feelepxyz/dass/docs/original-drawing/cutlist.png

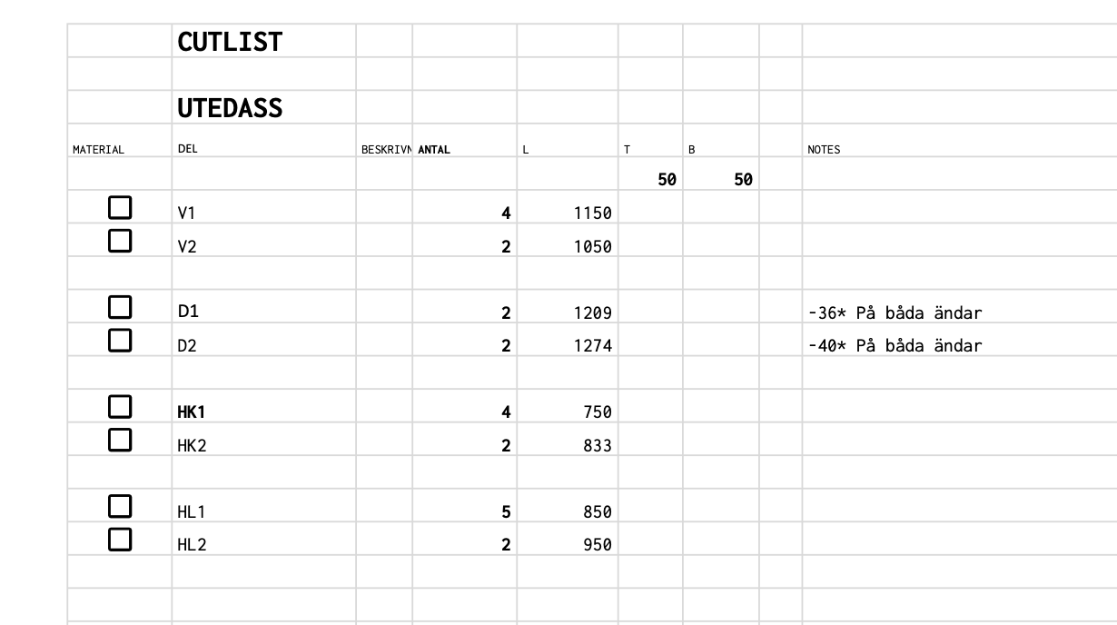
docs/original-drawing/cutlist.png
