feelepxyz/dass/docs/original-drawing/drawing-above.png

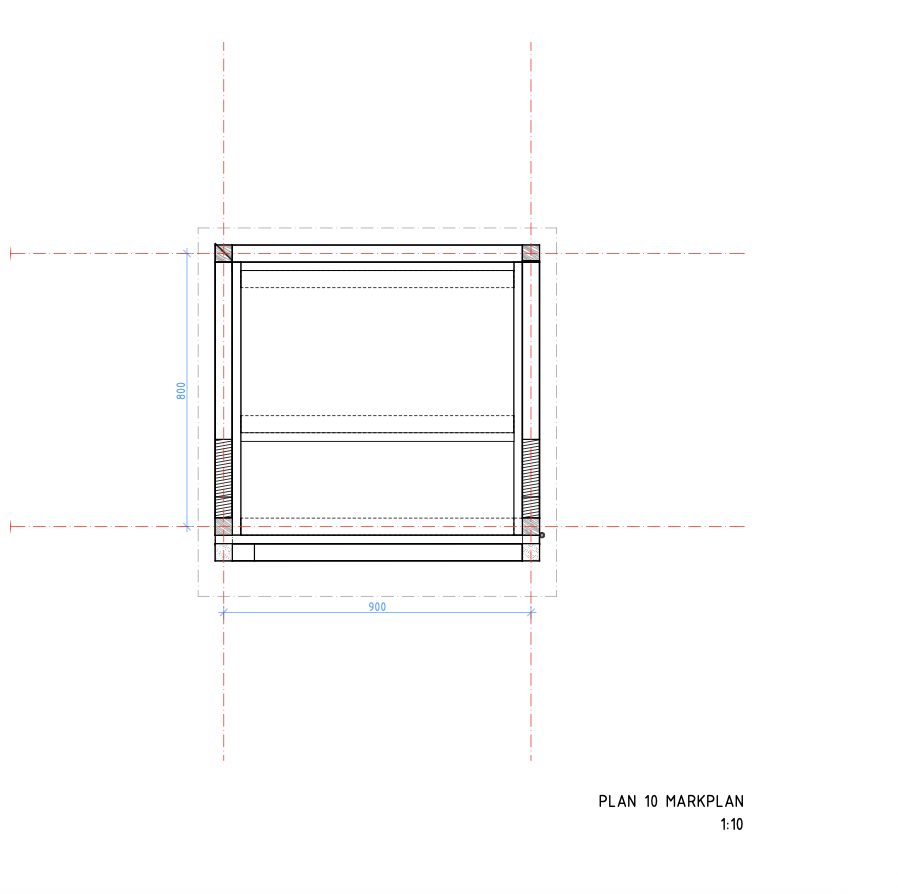
docs/original-drawing/drawing-above.png
