feelepxyz/dass/docs/original-drawing/render-target2.png

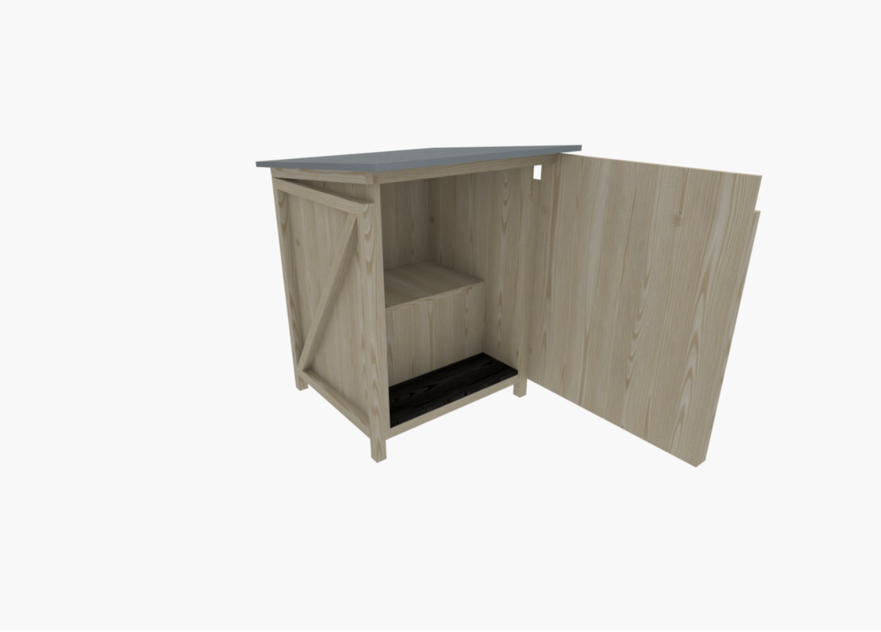
docs/original-drawing/render-target2.png
