feelepxyz/dass/docs/original-drawing/render-target.png

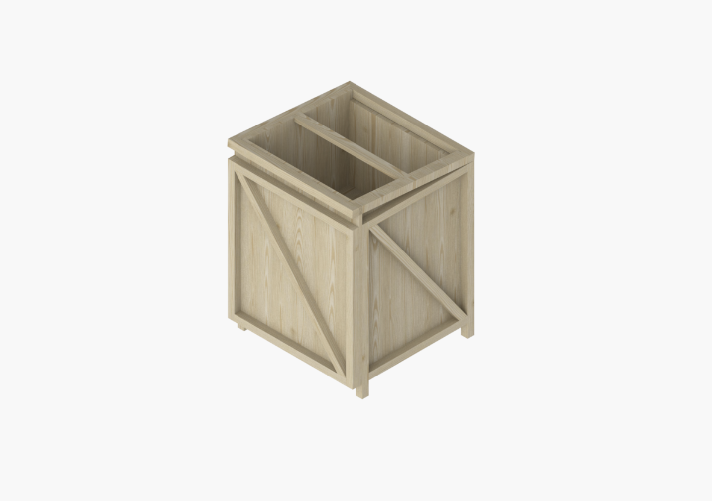
docs/original-drawing/render-target.png
