feelepxyz/dass/web/media/progress/cutting-poster.jpg

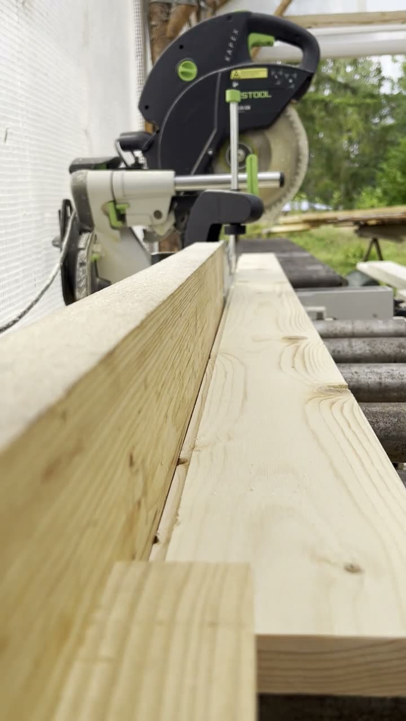
web/media/progress/cutting-poster.jpg
