feelepxyz/dass/web/media/progress/sides and floor.jpeg

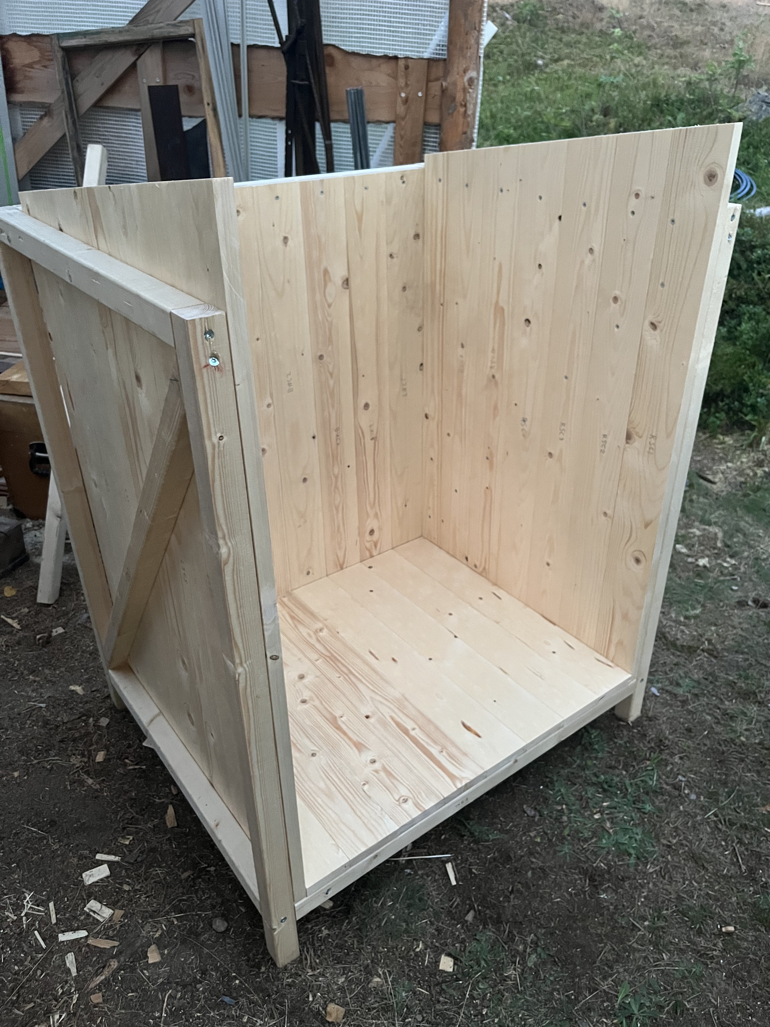
web/media/progress/sides and floor.jpeg
