feelepxyz/dass/build/dass-closed.png

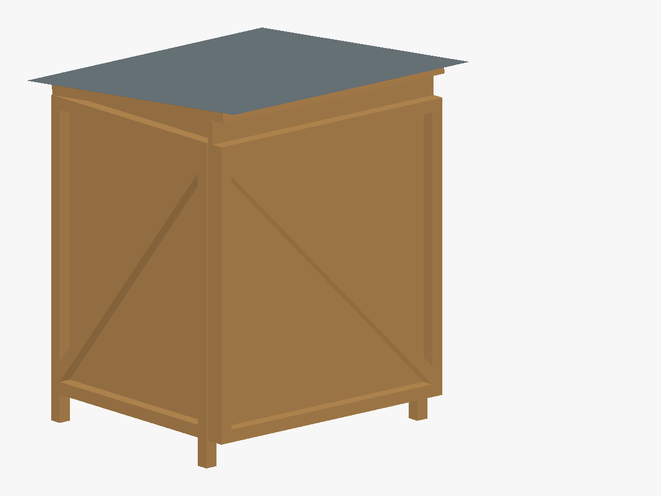
build/dass-closed.png
