feelepxyz/dass/build/dass-open.png

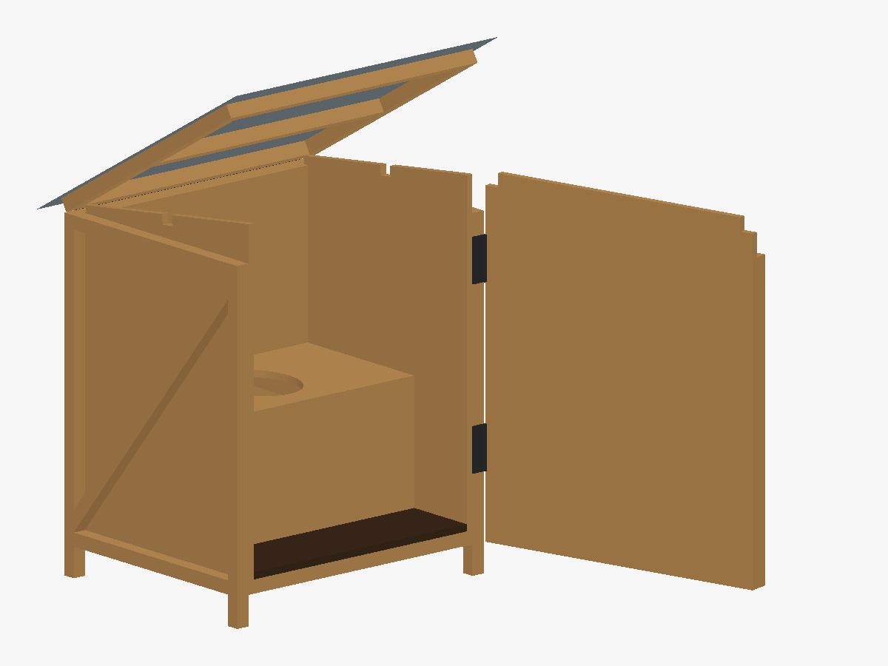
build/dass-open.png
