feelepxyz/dass/build/renders/closed-above.png

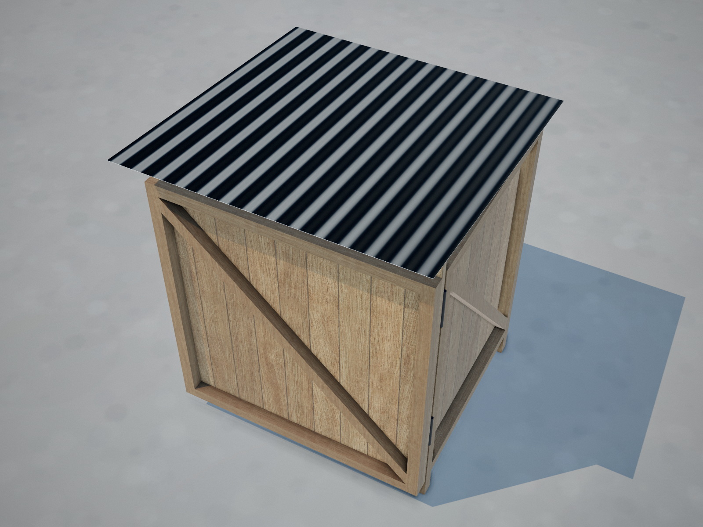
build/renders/closed-above.png
