feelepxyz/dass/build/renders/closed-front-left.png

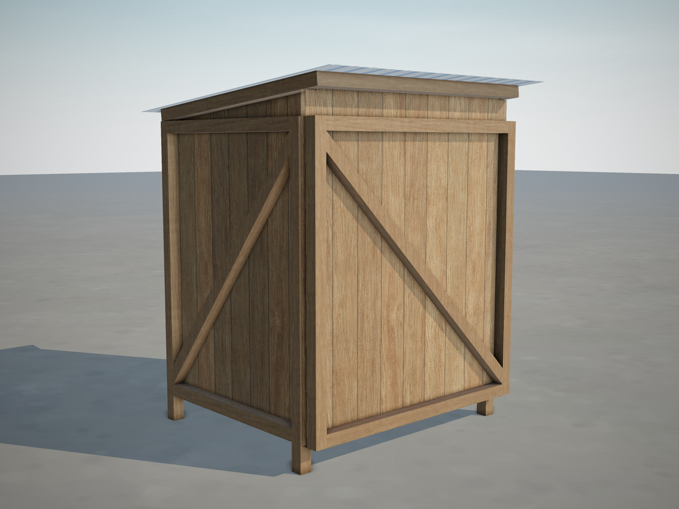
build/renders/closed-front-left.png
