feelepxyz/dass/build/renders/closed-hero.png

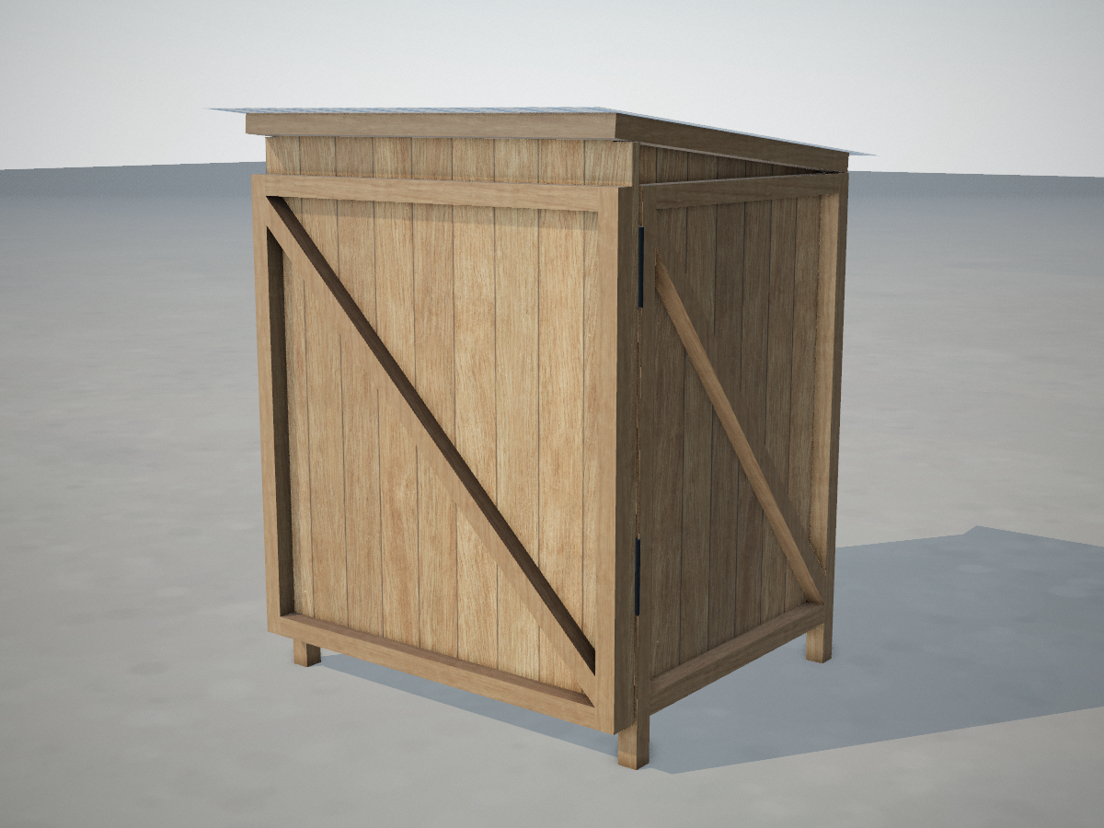
build/renders/closed-hero.png
