feelepxyz/dass/build/renders/closed-low.png

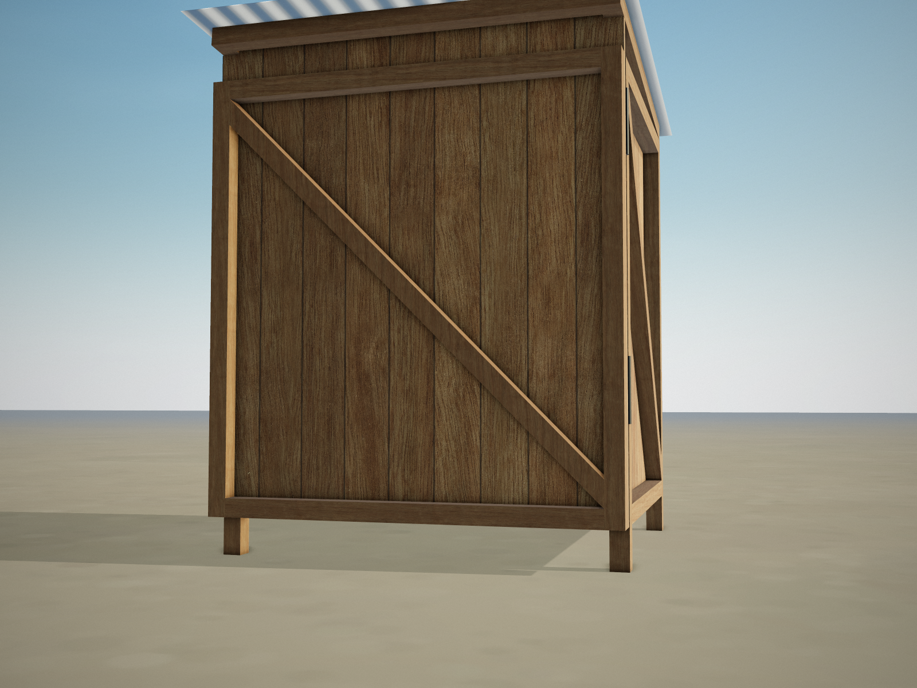
build/renders/closed-low.png
