feelepxyz/dass/build/renders/drawing-closed.png

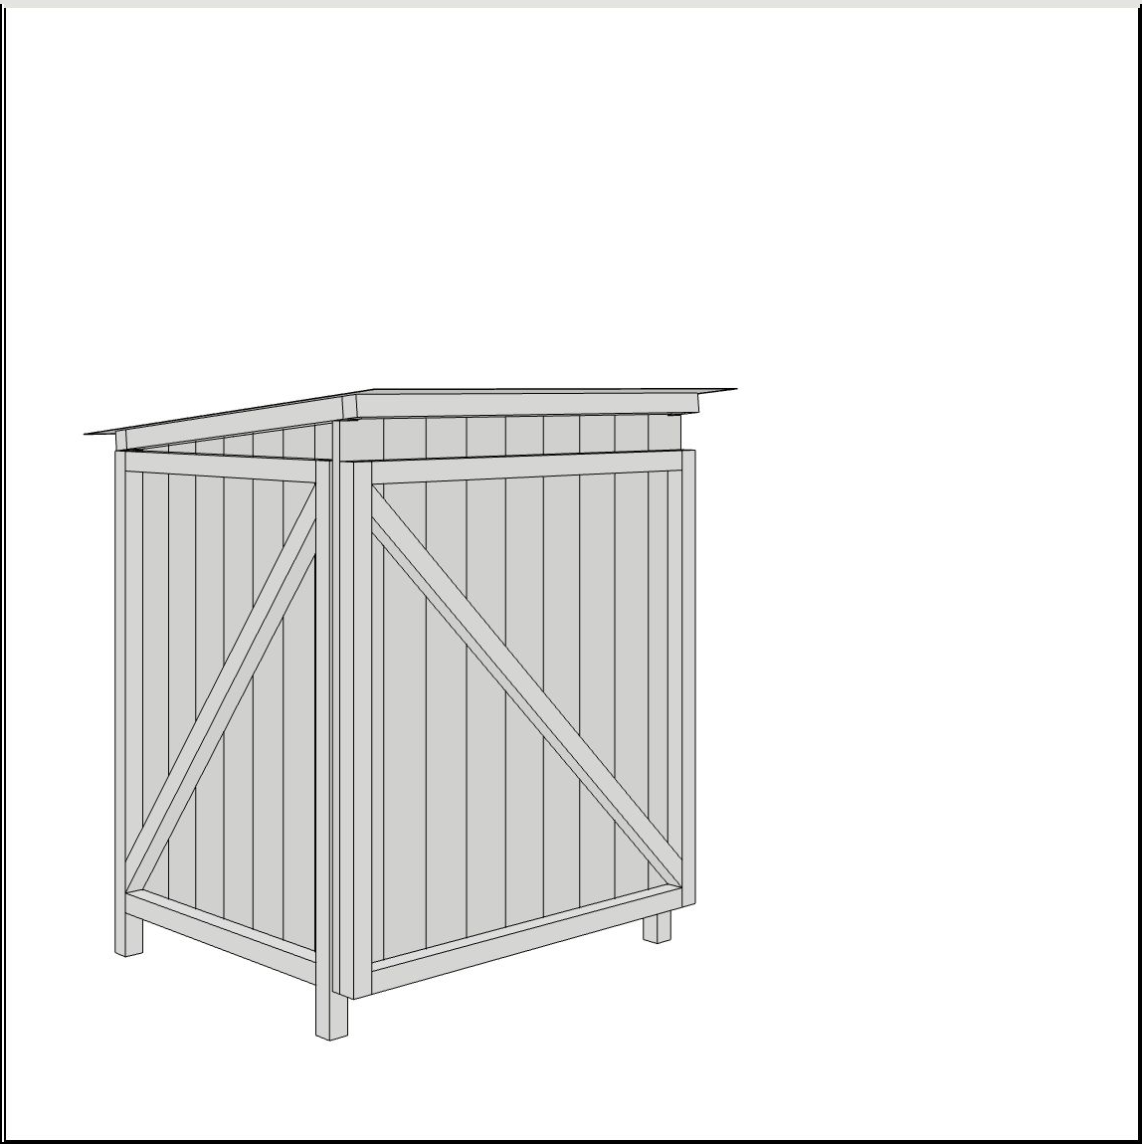
build/renders/drawing-closed.png
