feelepxyz/dass/build/renders/drawing-open.png

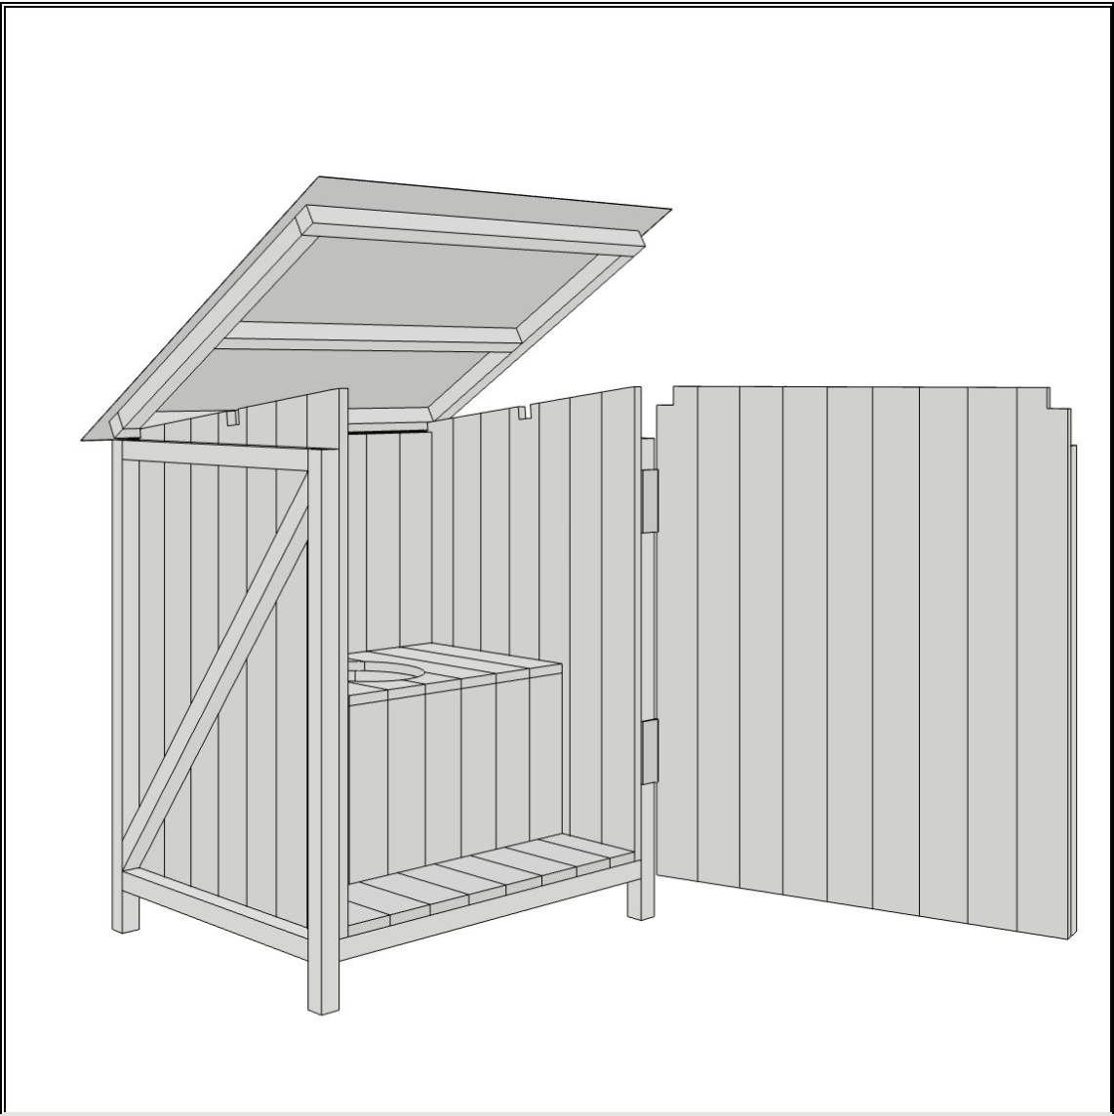
build/renders/drawing-open.png
