feelepxyz/dass/build/renders/flat-back.png

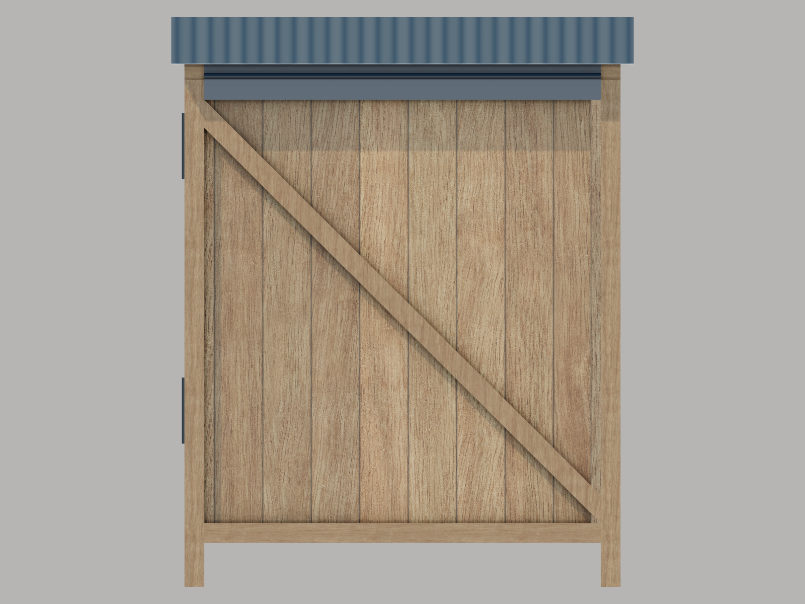
build/renders/flat-back.png
