feelepxyz/dass/build/renders/flat-bottom.png

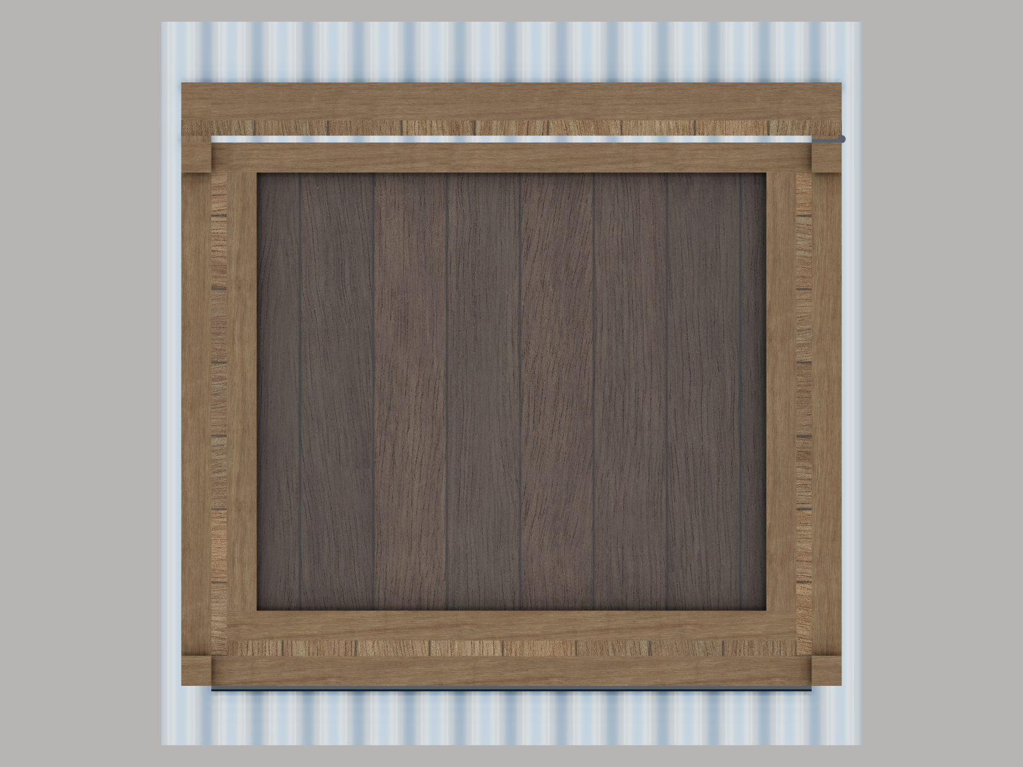
build/renders/flat-bottom.png
