feelepxyz/dass/build/renders/flat-front-open.png

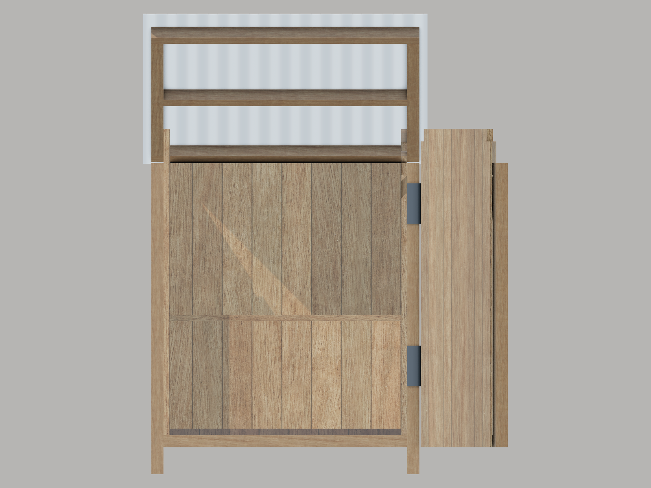
build/renders/flat-front-open.png
