feelepxyz/dass/build/renders/flat-front.png

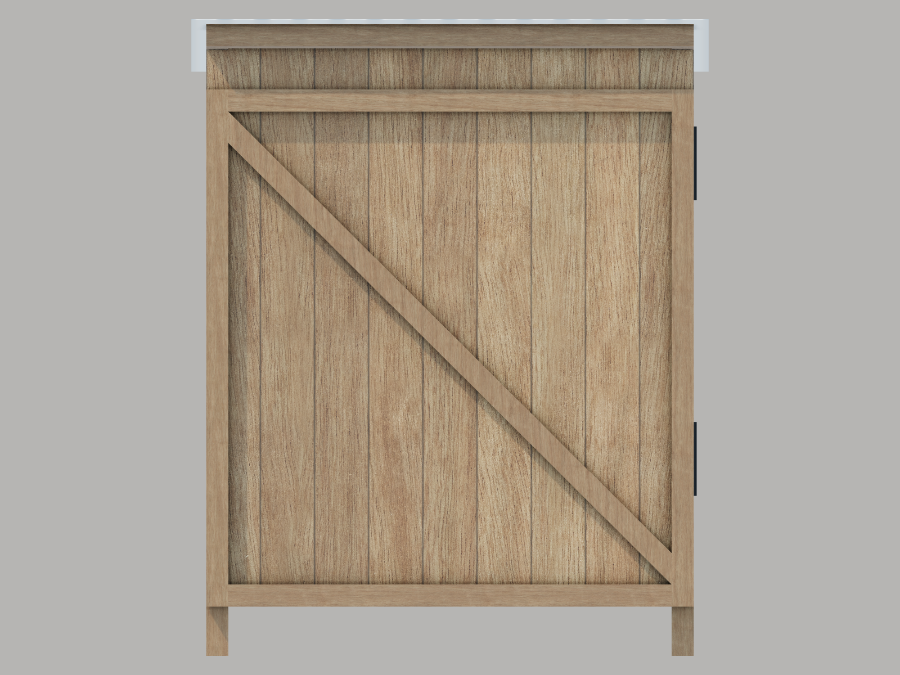
build/renders/flat-front.png
