feelepxyz/dass/build/renders/flat-left.png

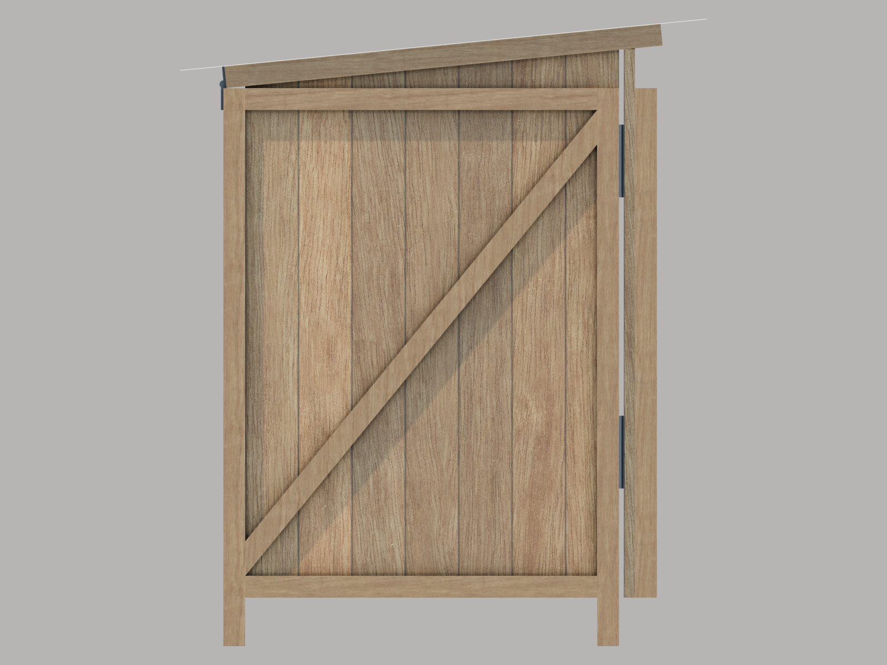
build/renders/flat-left.png
