feelepxyz/dass/build/renders/flat-right.png

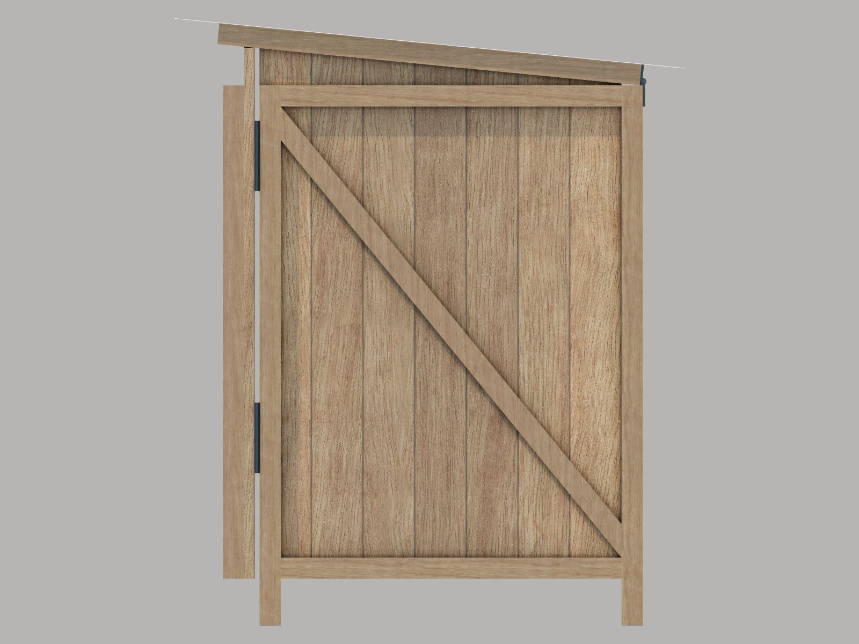
build/renders/flat-right.png
