feelepxyz/dass/build/renders/flat-top.png

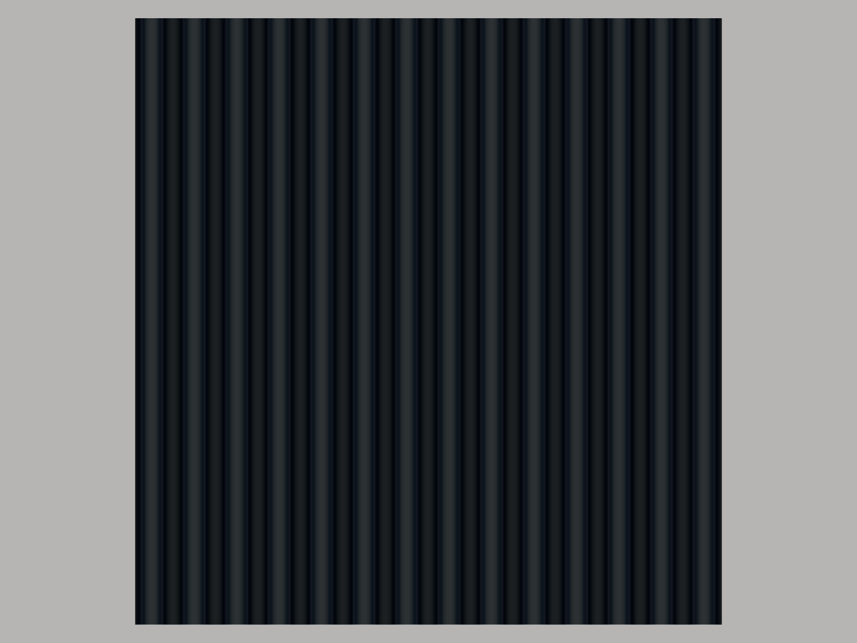
build/renders/flat-top.png
