feelepxyz/dass/build/renders/open-doorway.png

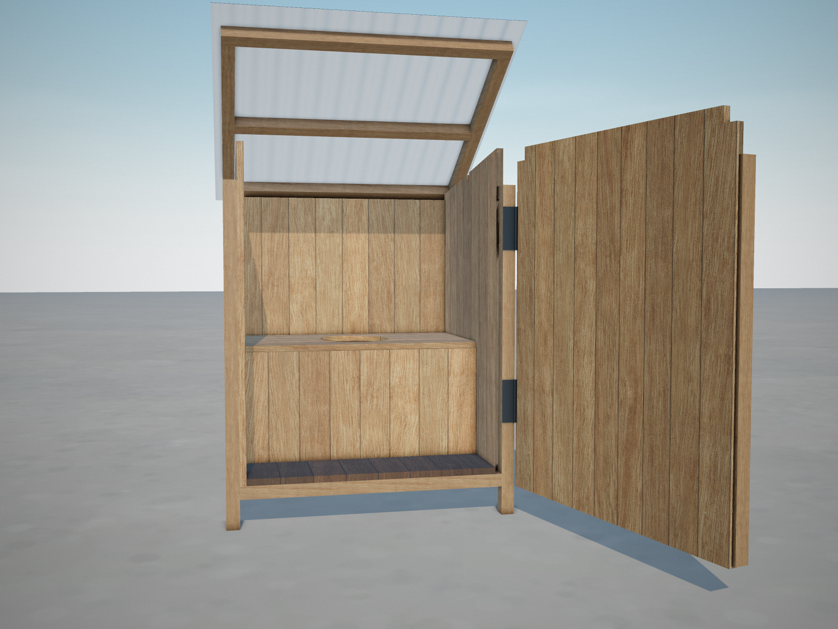
build/renders/open-doorway.png
