feelepxyz/dass/build/renders/open-hero.png

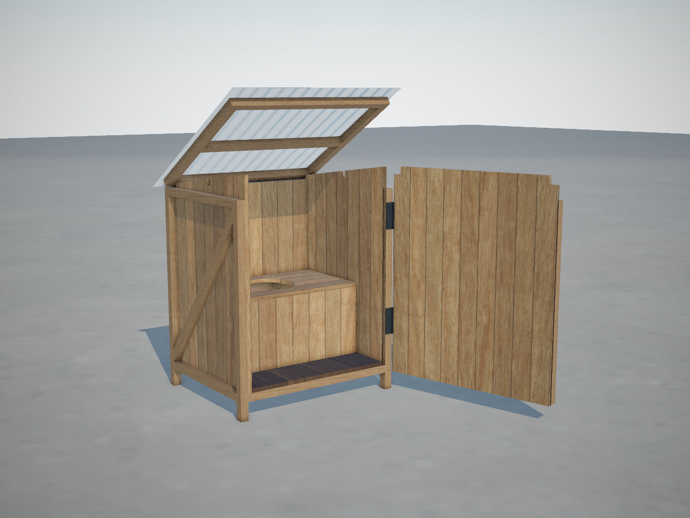
build/renders/open-hero.png
