feelepxyz/dass/build/renders/open-interior.png

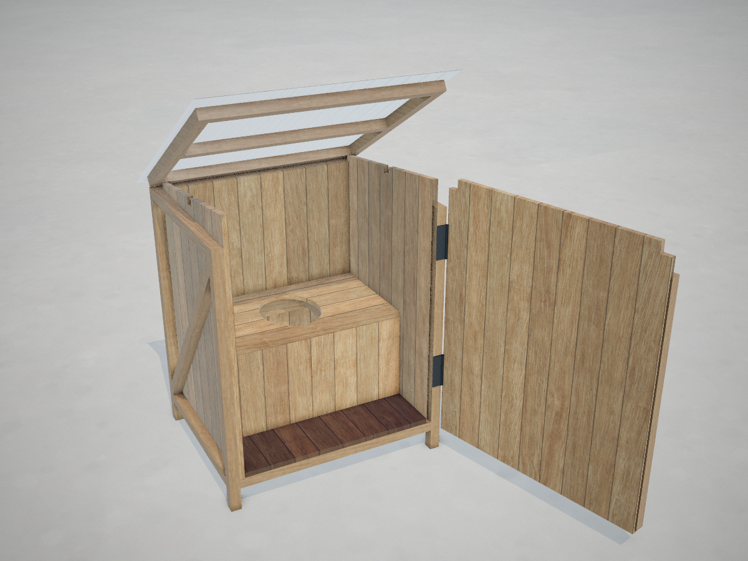
build/renders/open-interior.png
