feelepxyz/dass/build/renders/open-rear-quarter.png

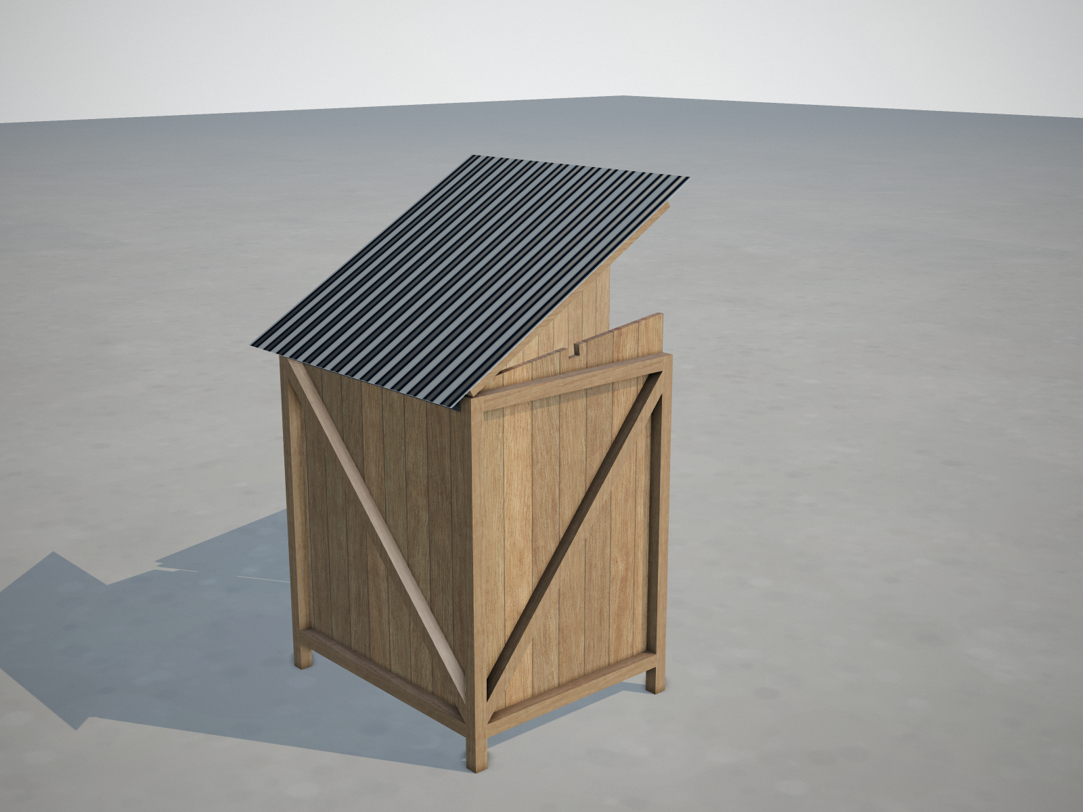
build/renders/open-rear-quarter.png
