feelepxyz/dass/build/renders/plank-roughness.png

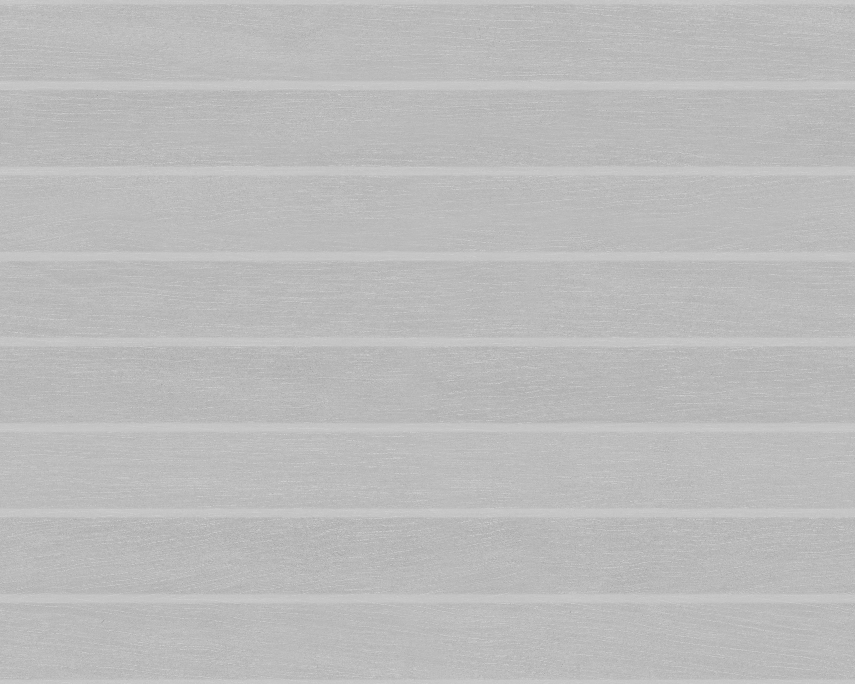
build/renders/plank-roughness.png
