feelepxyz/dass/build/renders/wood-birch.png

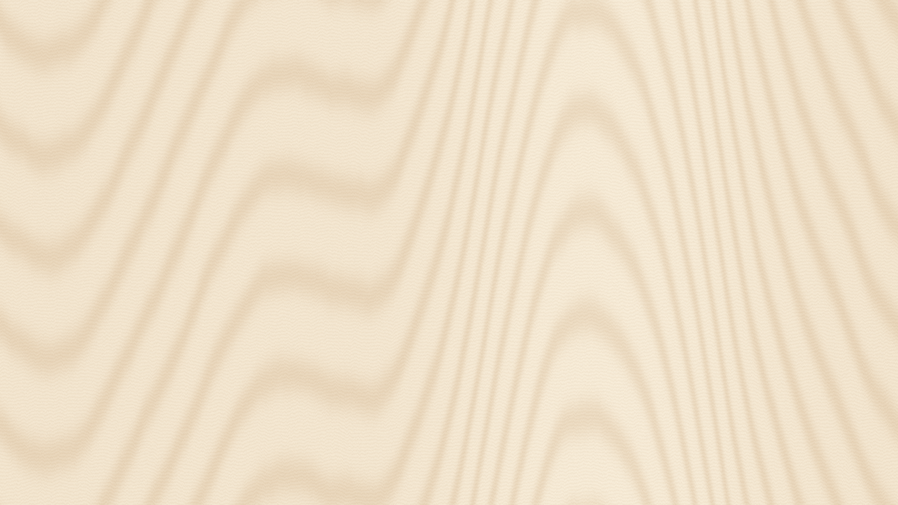
build/renders/wood-birch.png
