feelepxyz/dass/build/textures/plank-atlas.jpg

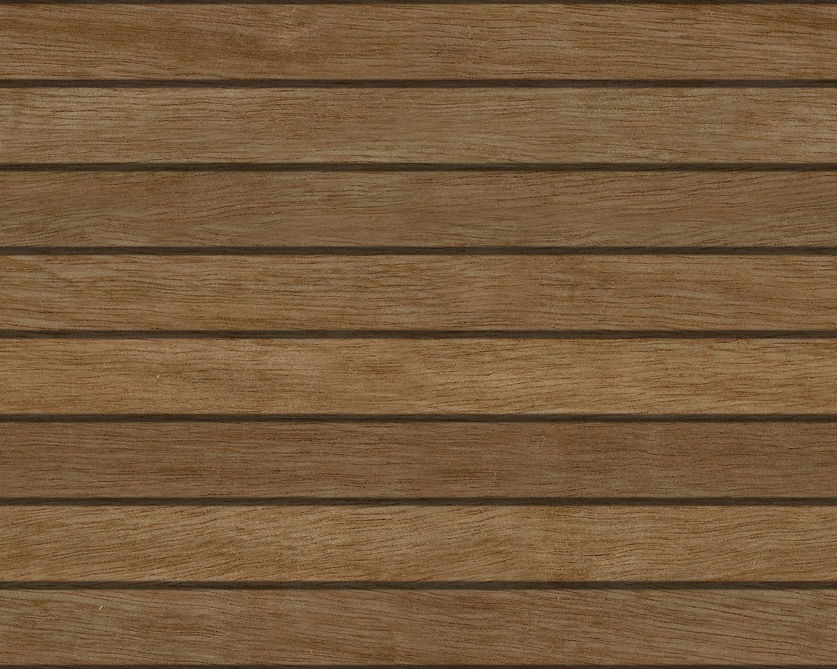
build/textures/plank-atlas.jpg
