feelepxyz/dass/build/textures/plank-normal.jpg

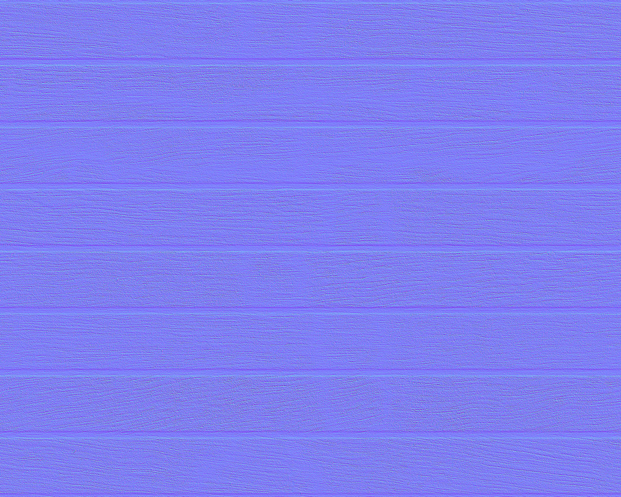
build/textures/plank-normal.jpg
