feelepxyz/dass/build/textures/wood-color.jpg

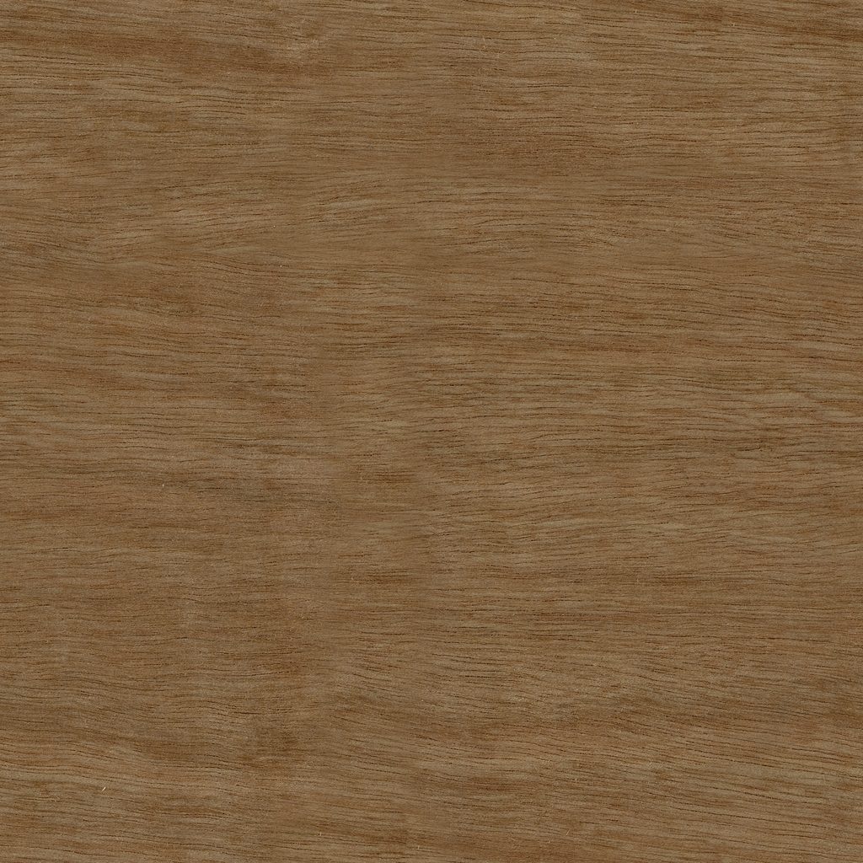
build/textures/wood-color.jpg
