feelepxyz/dass/build/web-renders/in-situ-closed.jpg

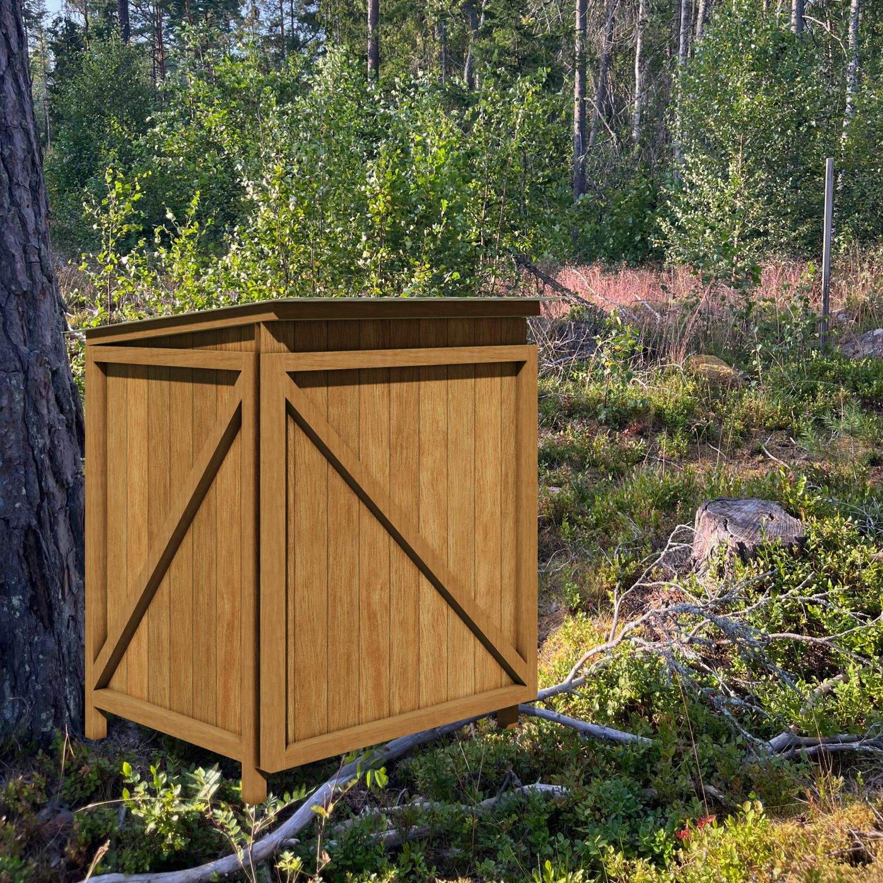
build/web-renders/in-situ-closed.jpg
