feelepxyz/dass/docs/verification/geometry/seat-box-assembly_20260802T100519Z.png

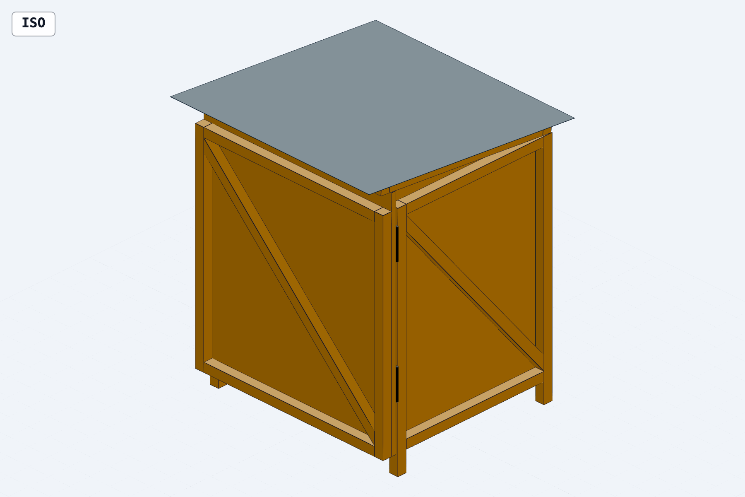
docs/verification/geometry/seat-box-assembly_20260802T100519Z.png
