feelepxyz/dass/docs/verification/guide/shots/assembly-1440.png

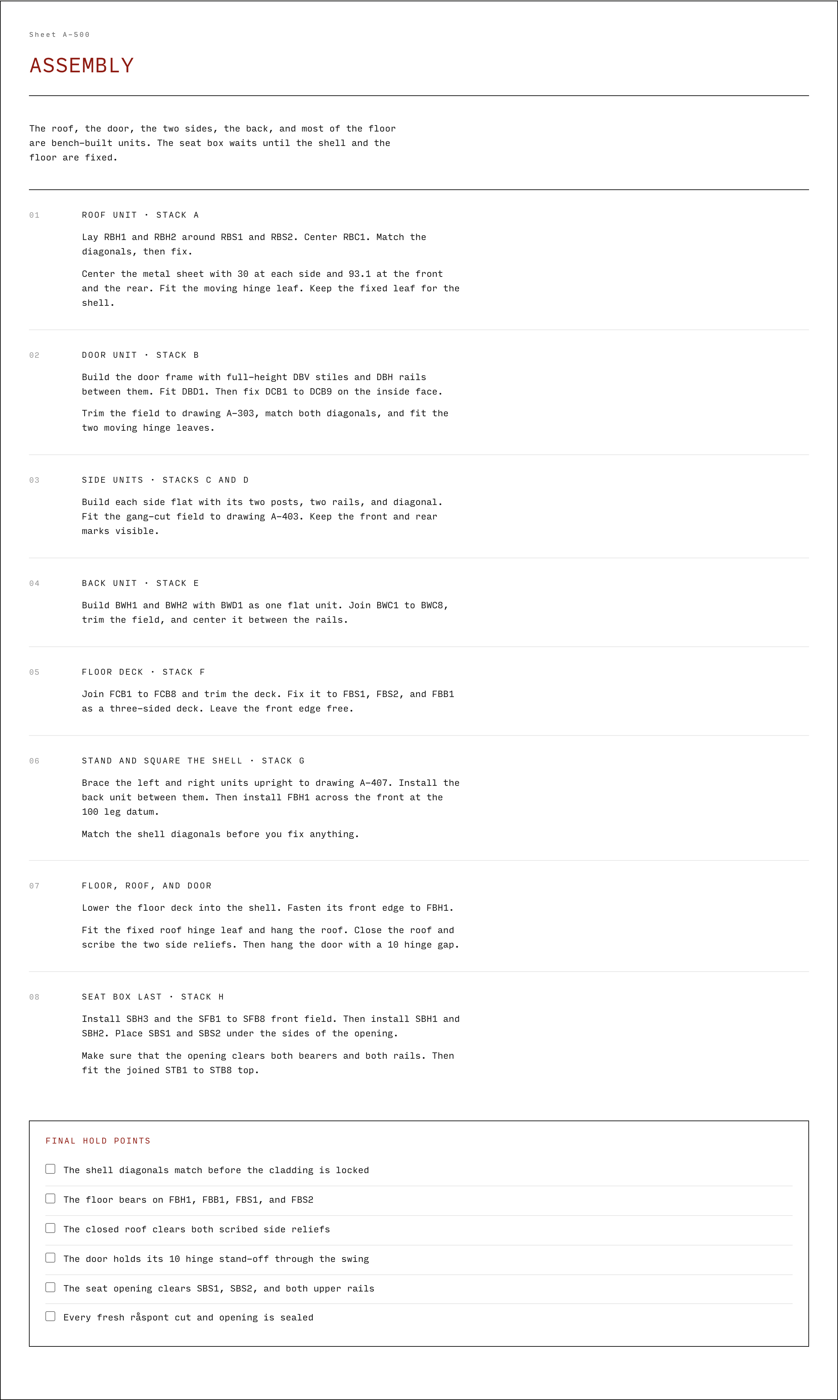
docs/verification/guide/shots/assembly-1440.png
