feelepxyz/dass/docs/verification/guide/shots/beams-1440.png

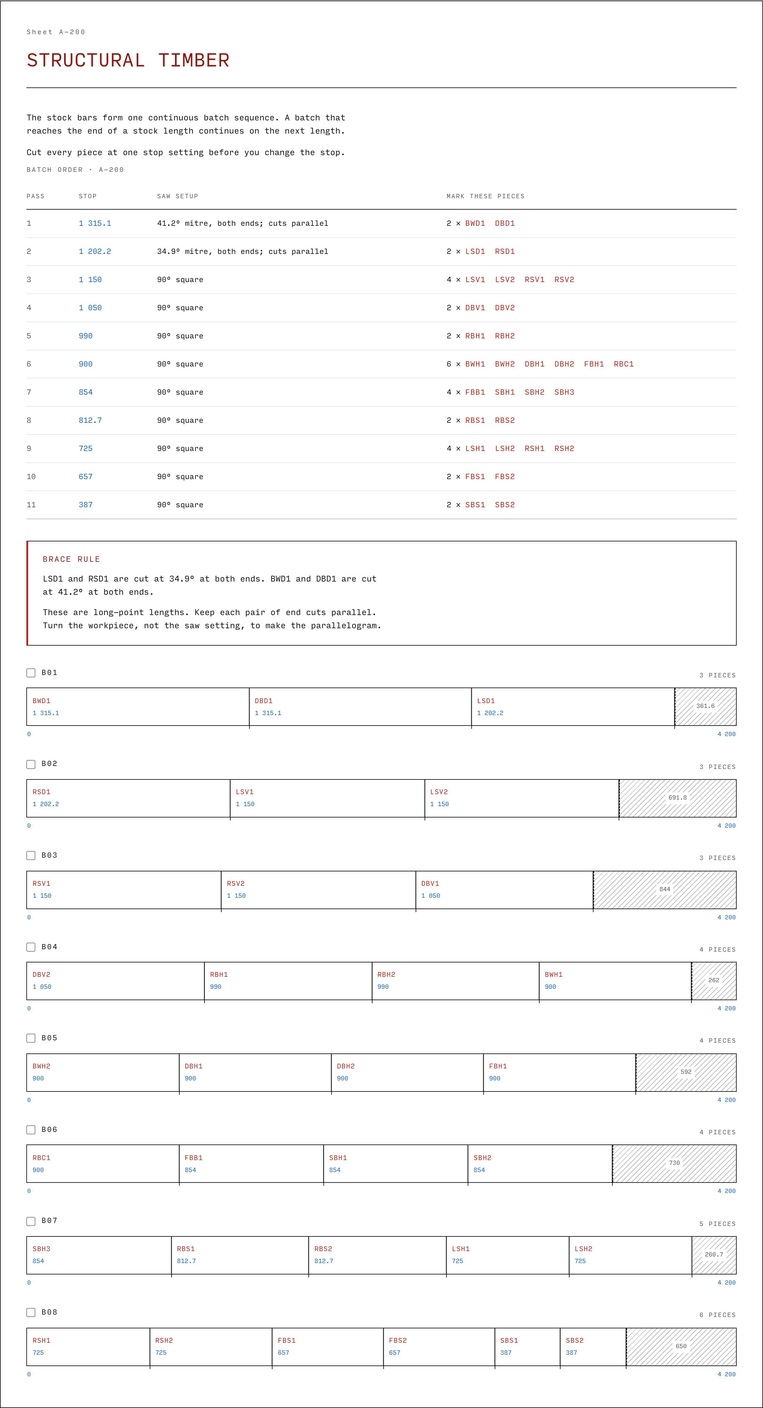
docs/verification/guide/shots/beams-1440.png
