feelepxyz/dass/docs/verification/guide/shots/drawing-1440.png

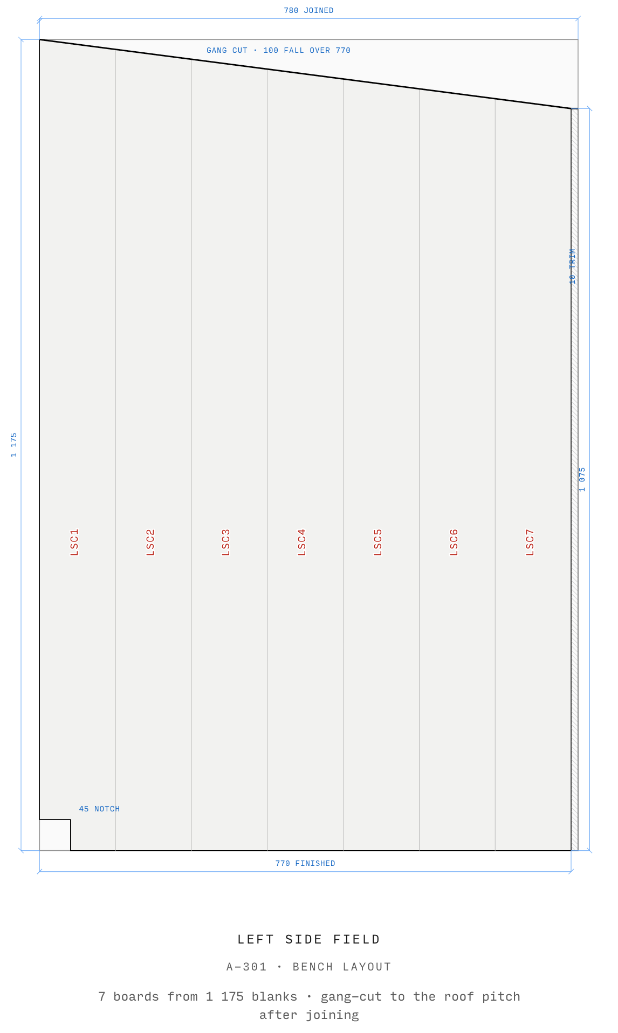
docs/verification/guide/shots/drawing-1440.png
