feelepxyz/dass/docs/verification/guide/shots/drawing-open-against-unit-plate.png

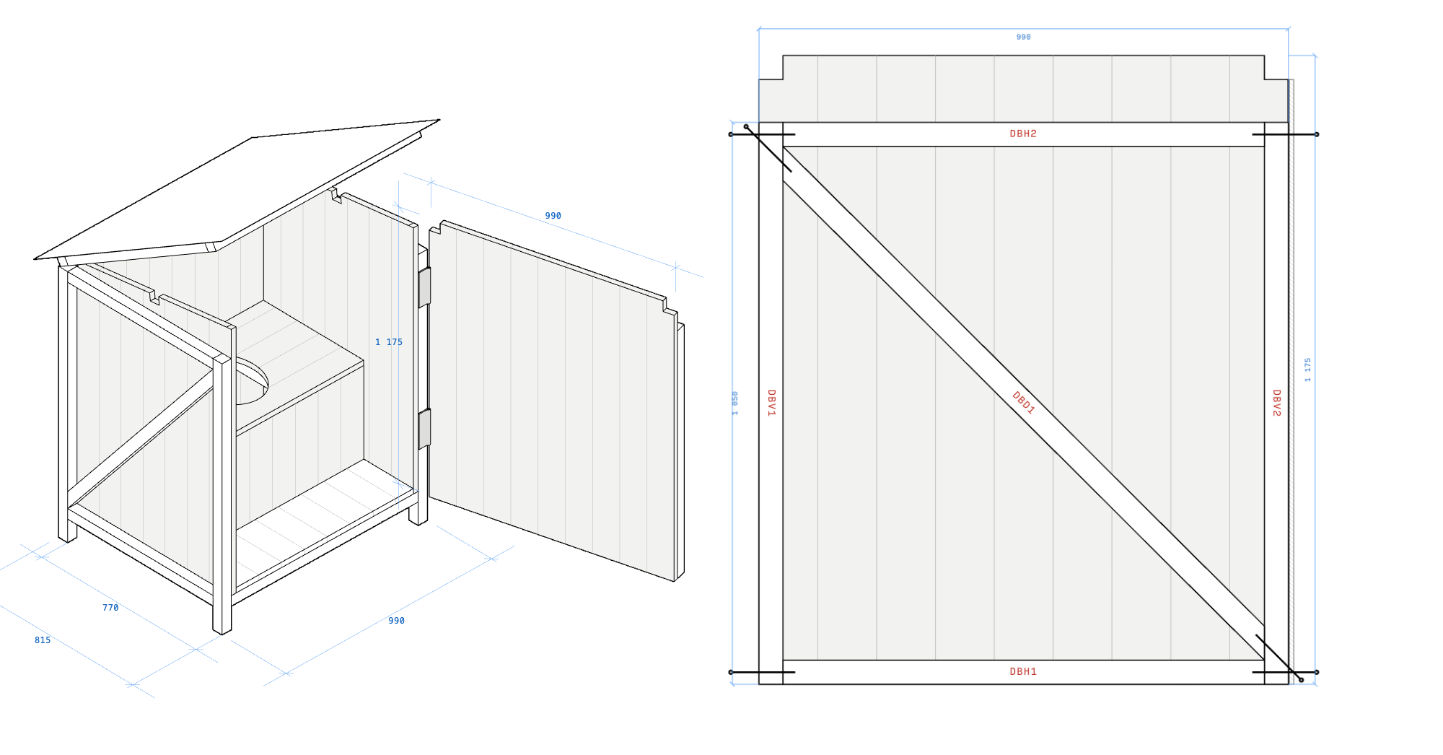
docs/verification/guide/shots/drawing-open-against-unit-plate.png
