feelepxyz/dass/docs/verification/guide/shots/drawing-open-isometric.png

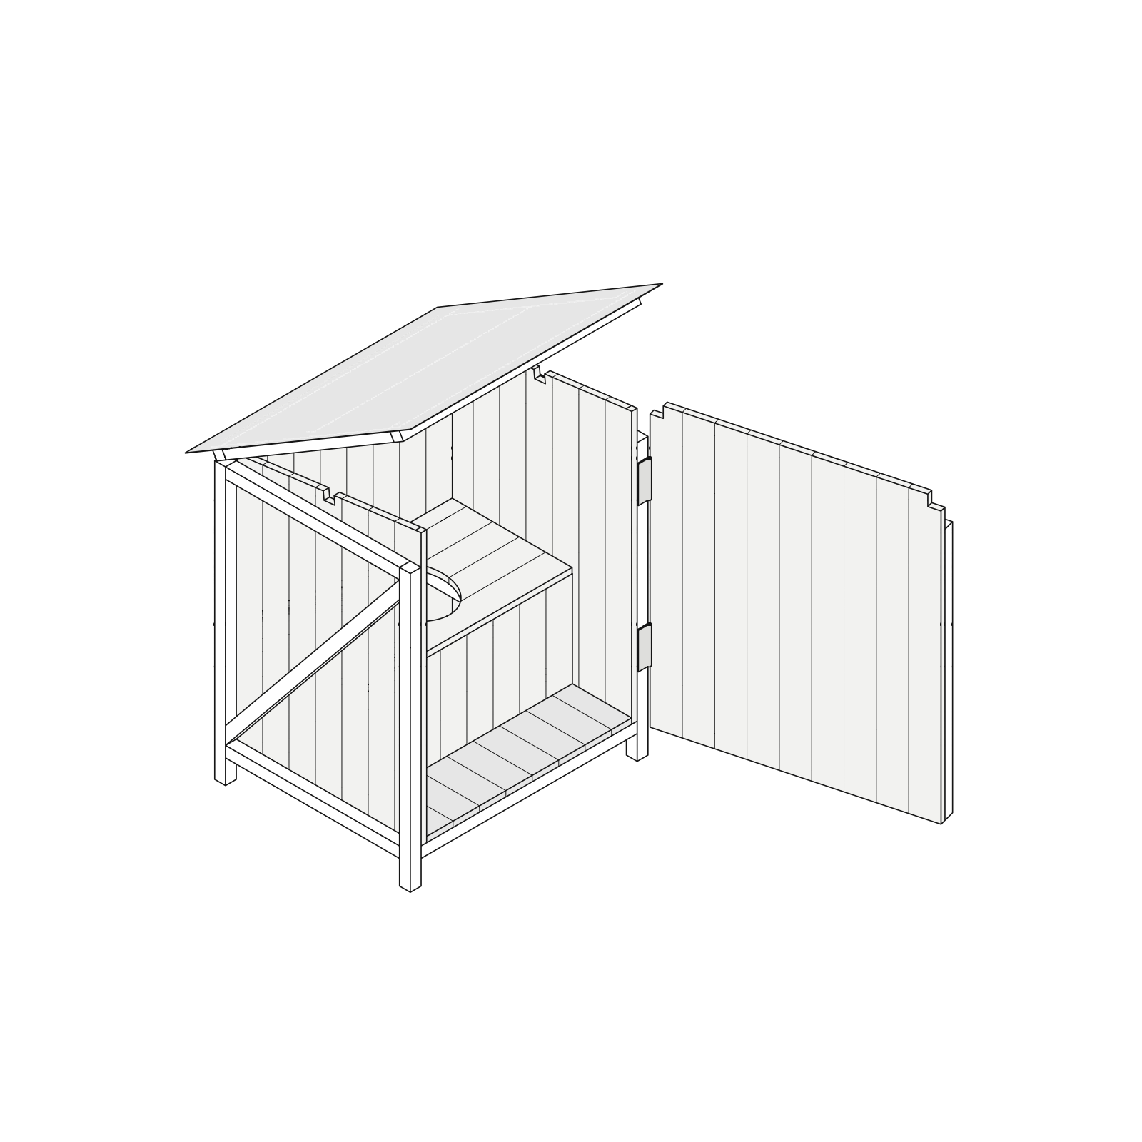
docs/verification/guide/shots/drawing-open-isometric.png
