feelepxyz/dass/docs/verification/guide/shots/method-1440.png

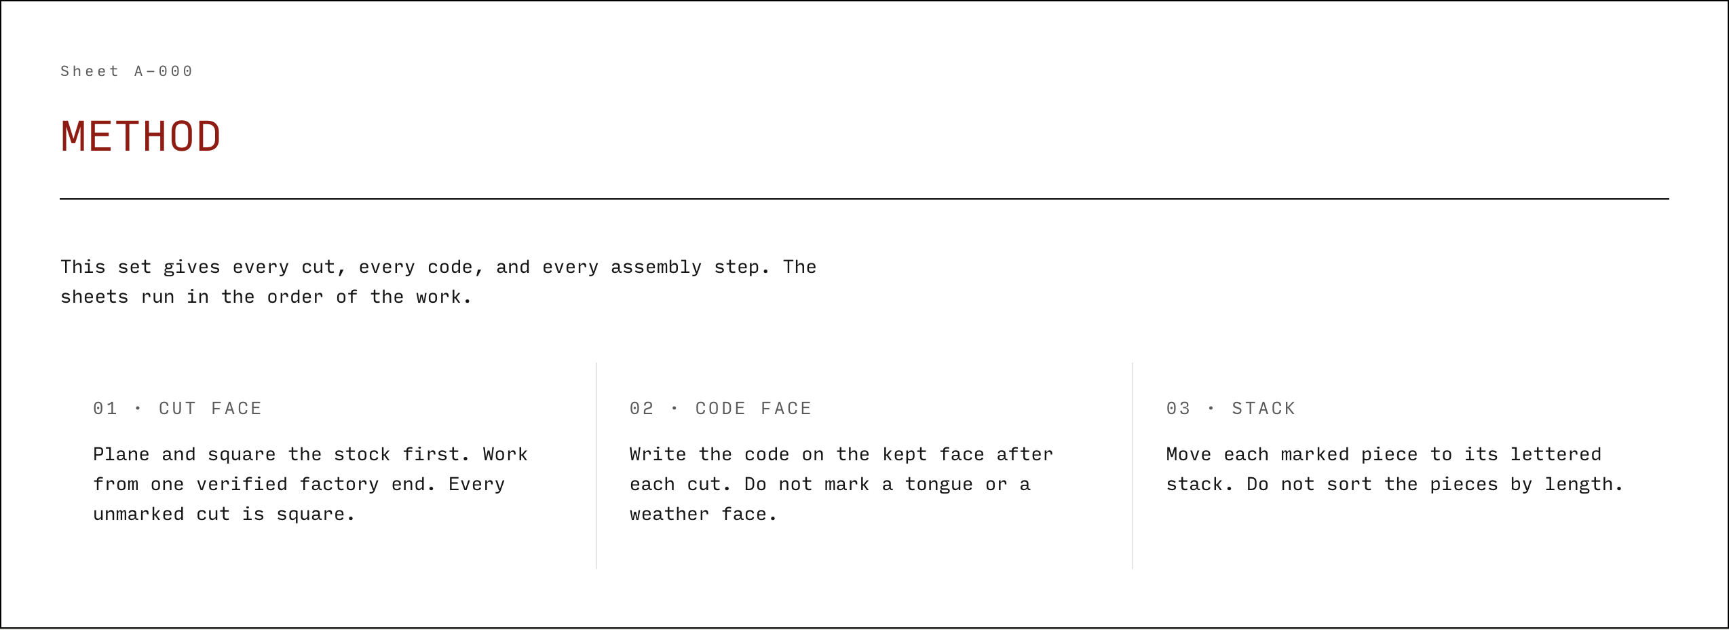
docs/verification/guide/shots/method-1440.png
