feelepxyz/dass/docs/verification/guide/shots/register-1440.png

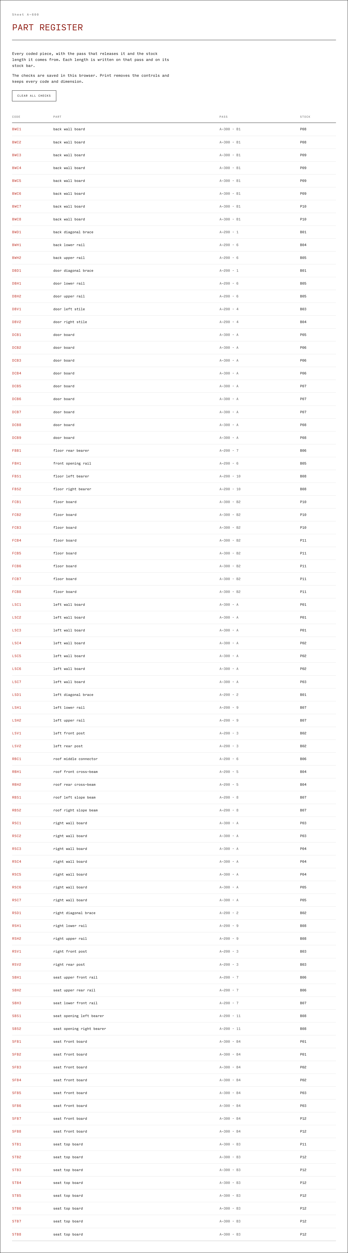
docs/verification/guide/shots/register-1440.png
