feelepxyz/dass/docs/verification/guide/shots/registration-1440.png

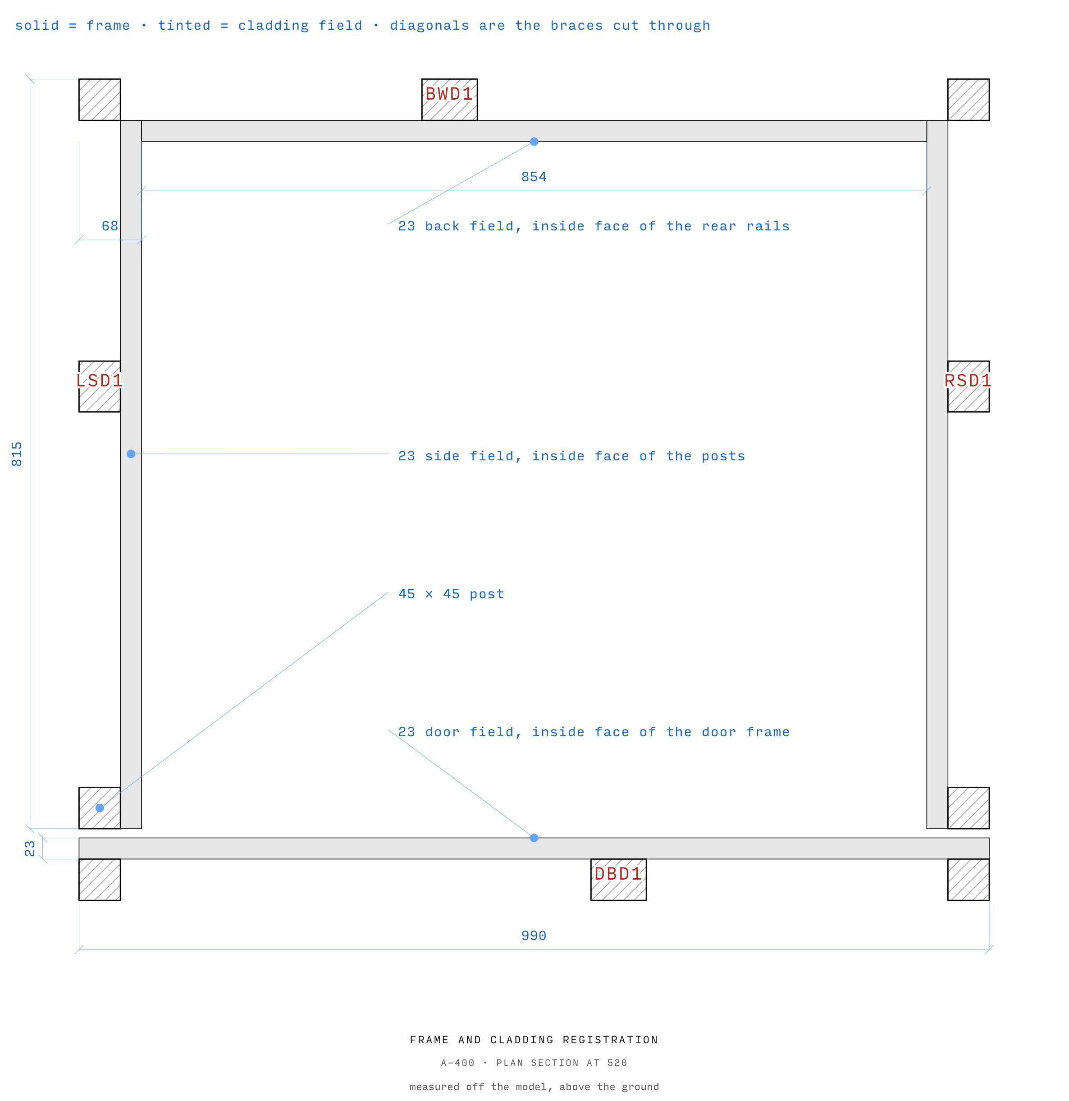
docs/verification/guide/shots/registration-1440.png
