feelepxyz/dass/docs/verification/guide/shots/render-390.png

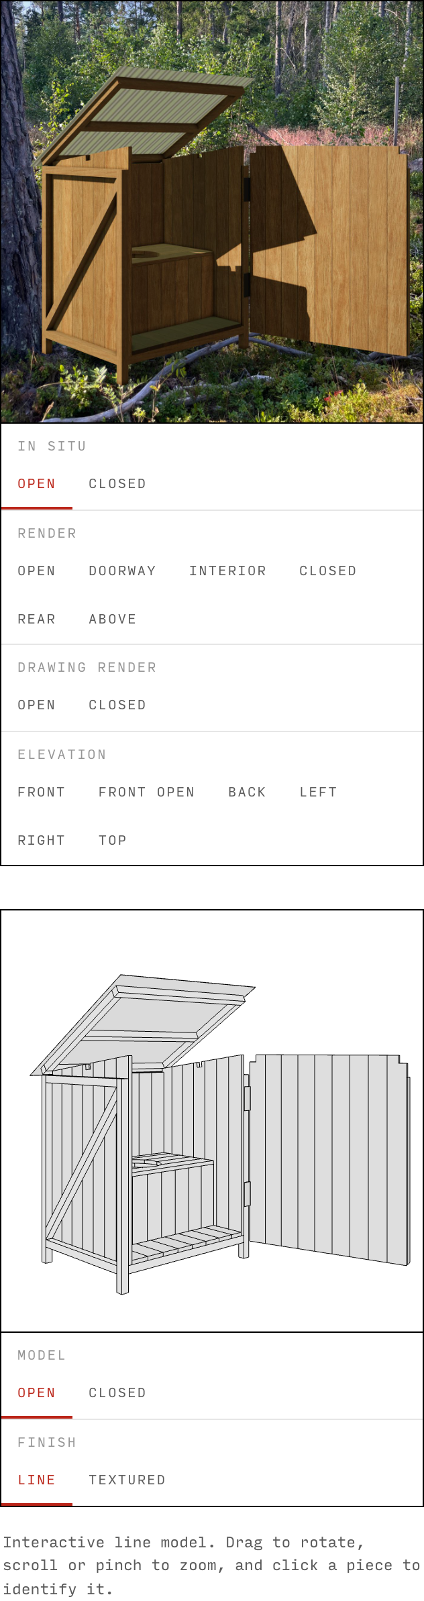
docs/verification/guide/shots/render-390.png
