feelepxyz/dass/docs/verification/guide/shots/render-900.png

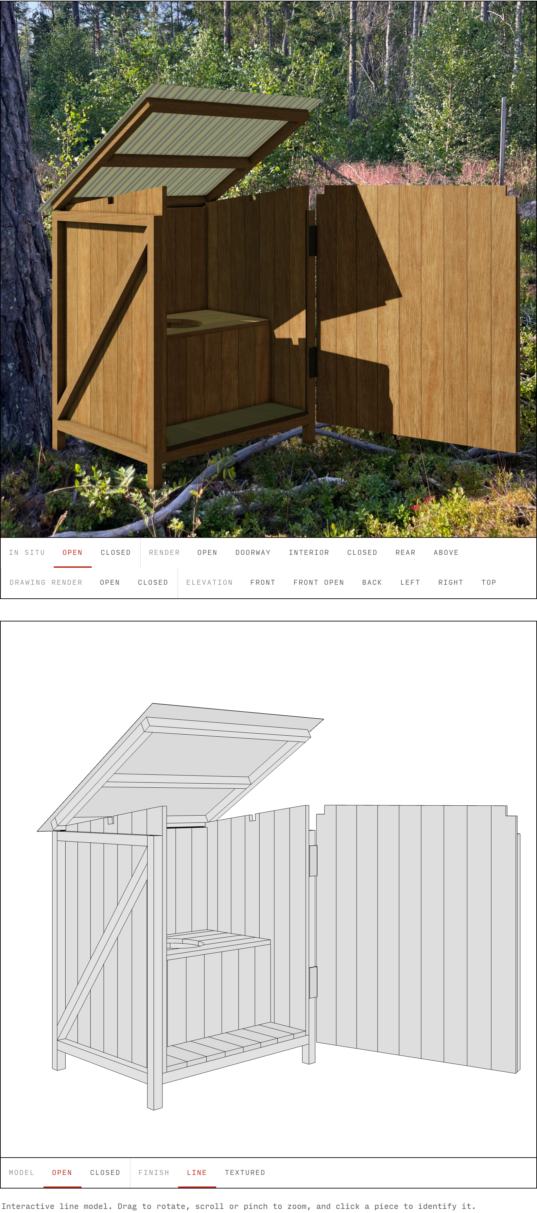
docs/verification/guide/shots/render-900.png
