feelepxyz/dass/docs/verification/guide/shots/render-1440.png

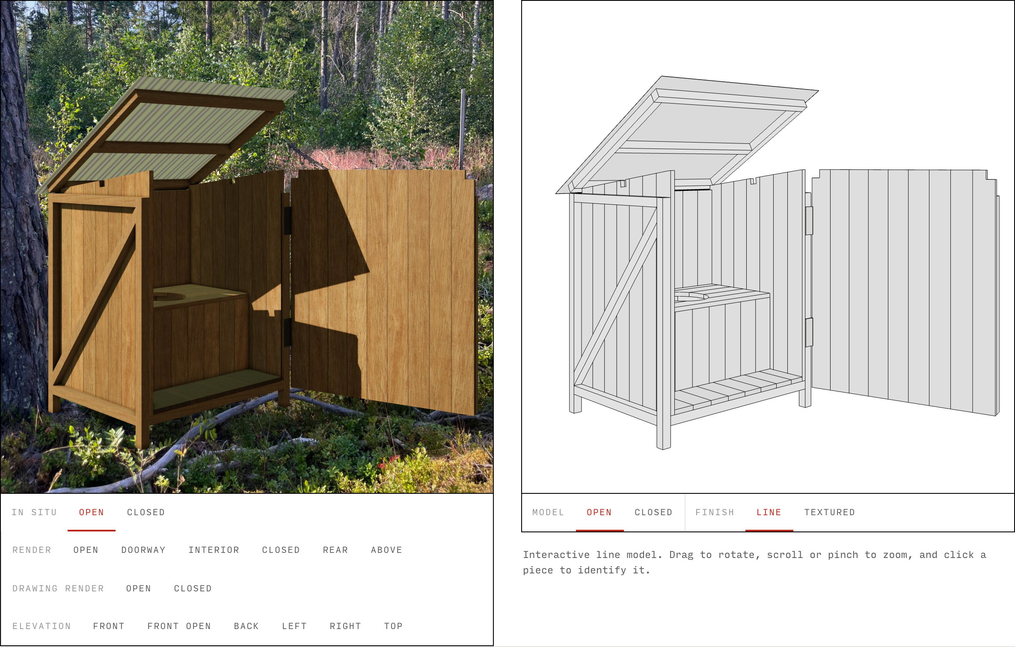
docs/verification/guide/shots/render-1440.png
