feelepxyz/dass/docs/verification/guide/shots/set-foot-1440.png

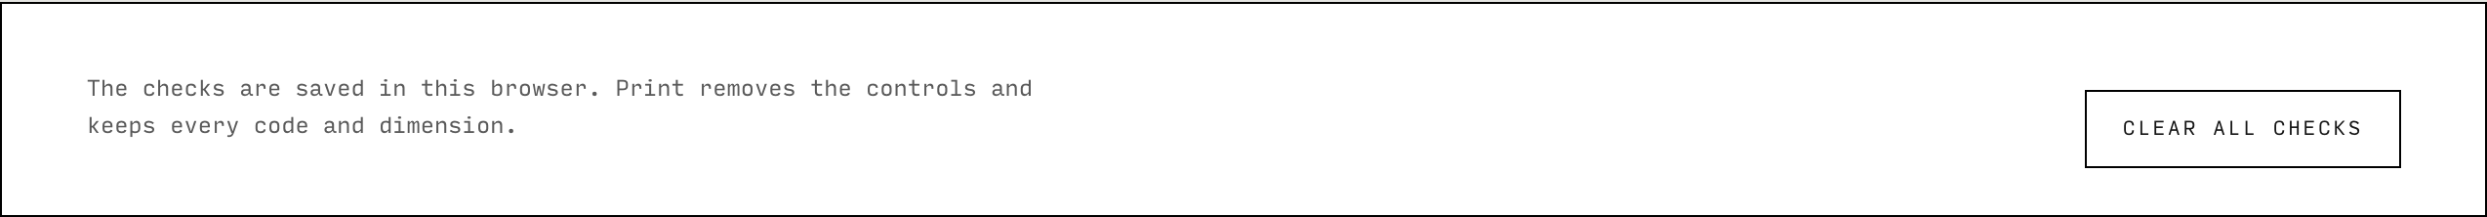
docs/verification/guide/shots/set-foot-1440.png
