feelepxyz/dass/docs/verification/guide/shots/top-1440.png

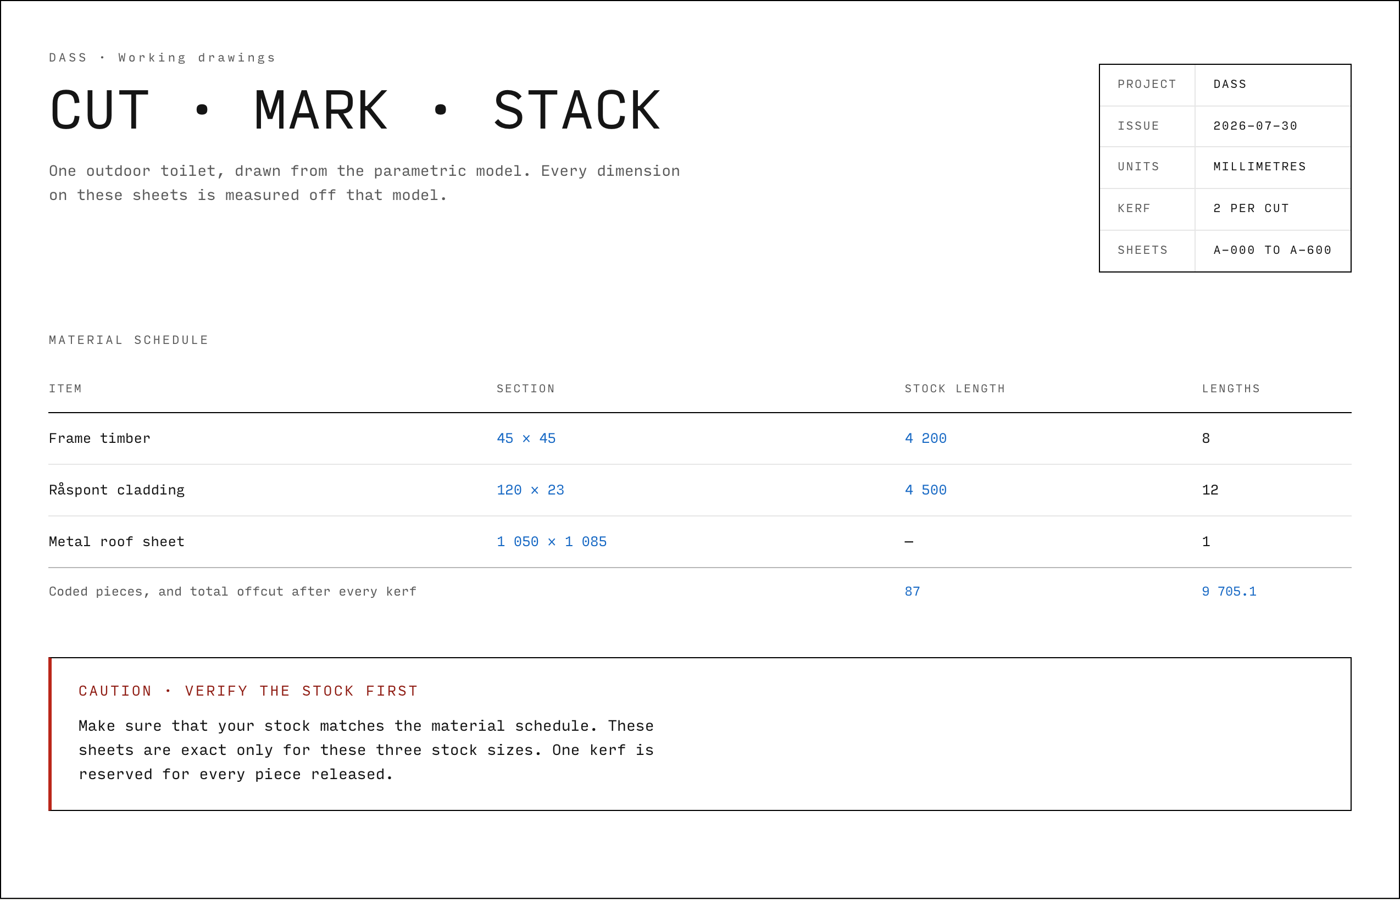
docs/verification/guide/shots/top-1440.png
