feelepxyz/dass/docs/verification/guide/shots/unit-c-1440.png

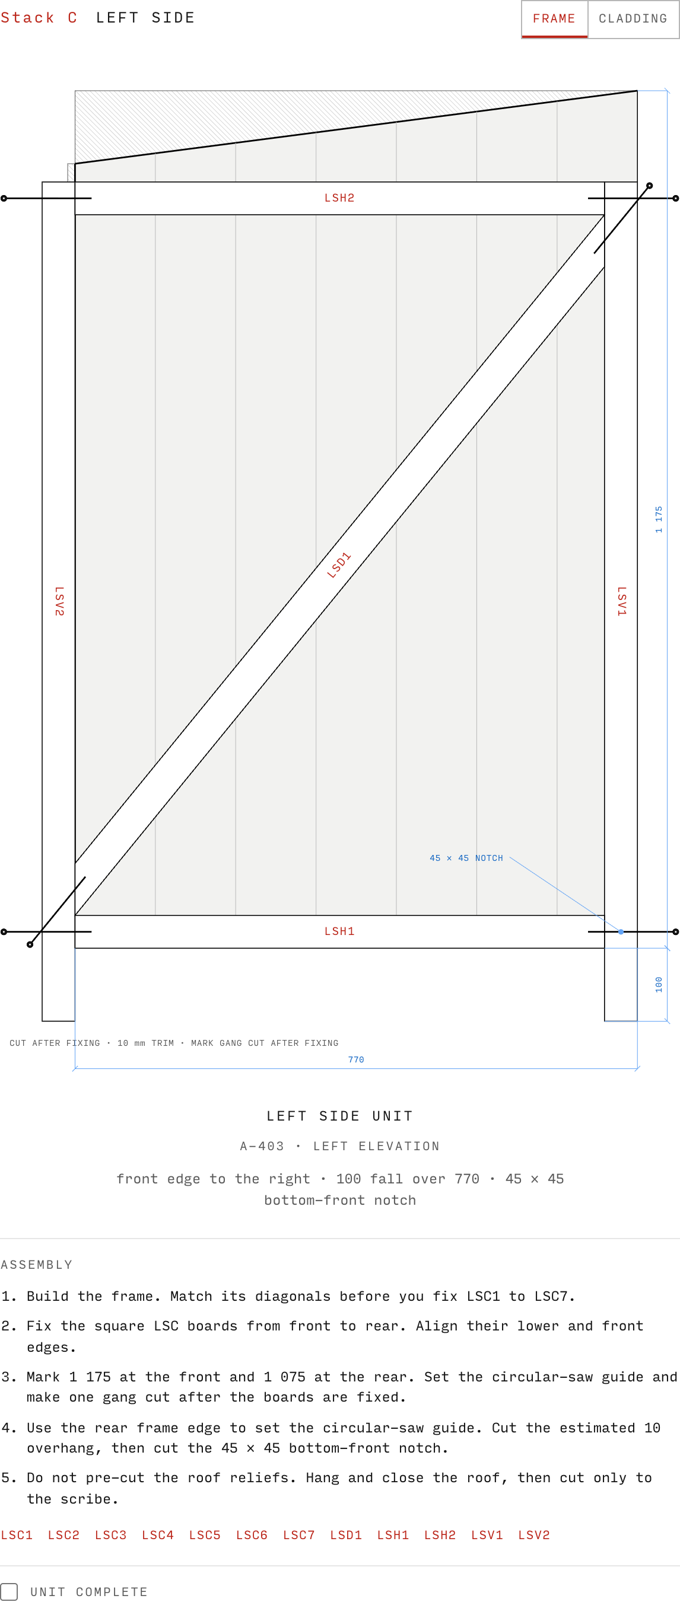
docs/verification/guide/shots/unit-c-1440.png
