feelepxyz/dass/docs/verification/guide/shots/unit-c-cladding-1440.png

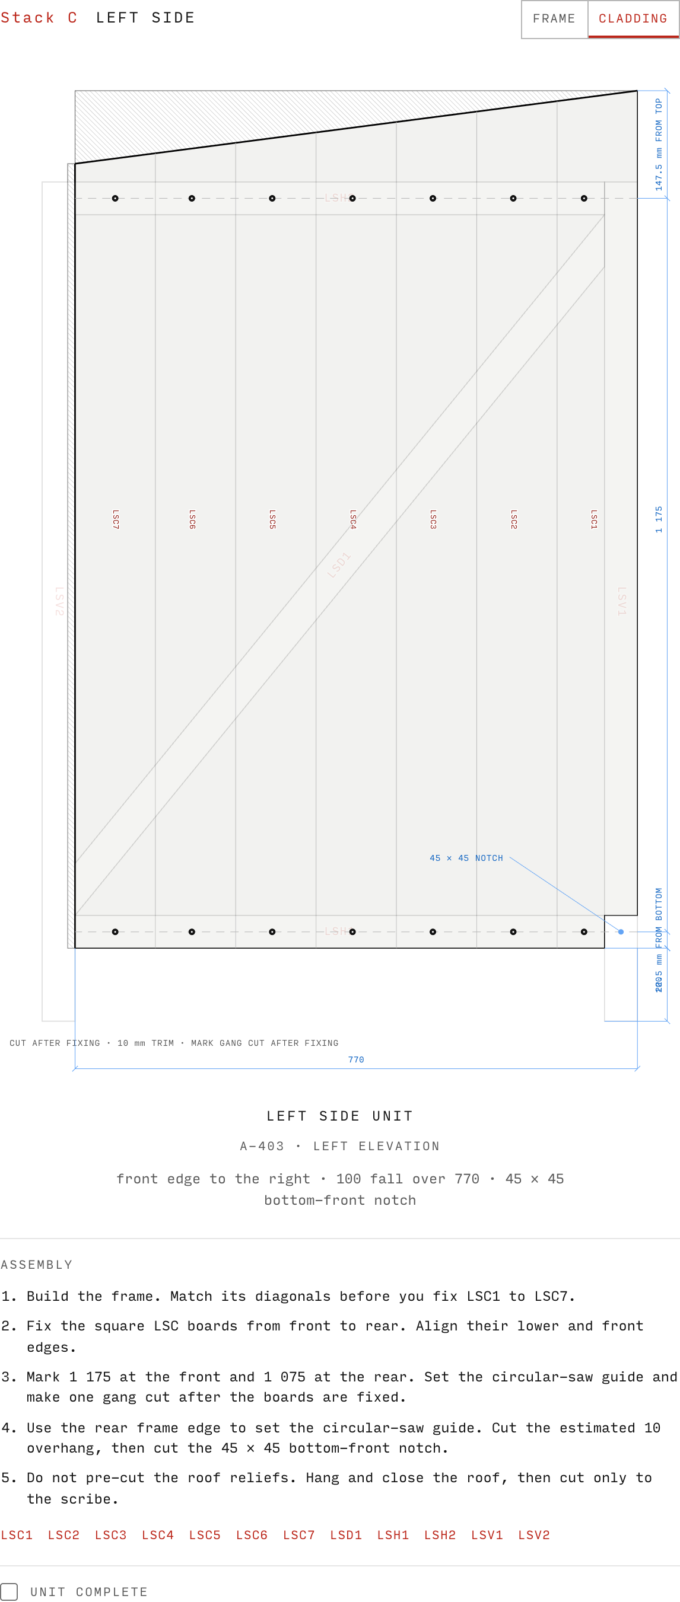
docs/verification/guide/shots/unit-c-cladding-1440.png
