feelepxyz/dass/docs/verification/guide/shots/unit-d-1440.png

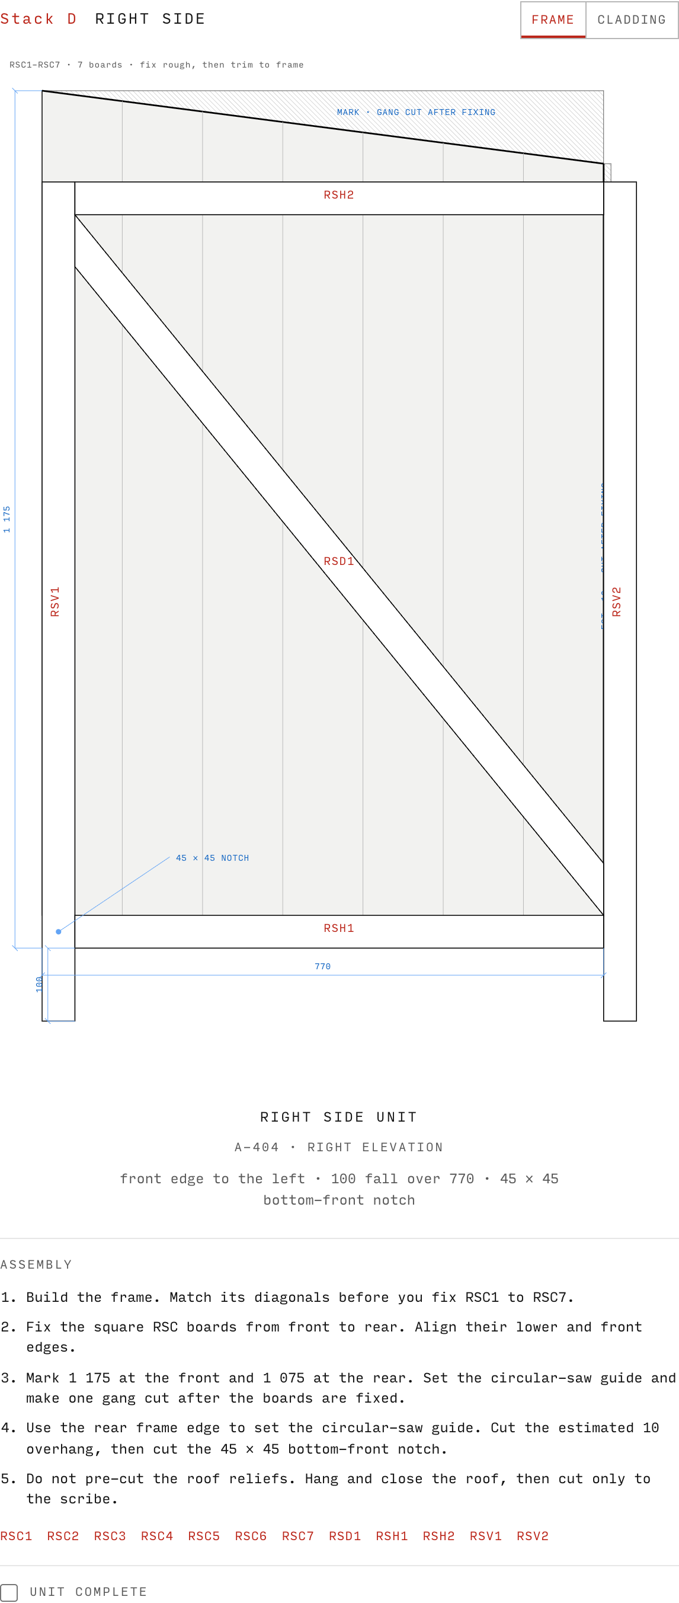
docs/verification/guide/shots/unit-d-1440.png
