feelepxyz/dass/docs/verification/guide/shots/unit-e-1440.png

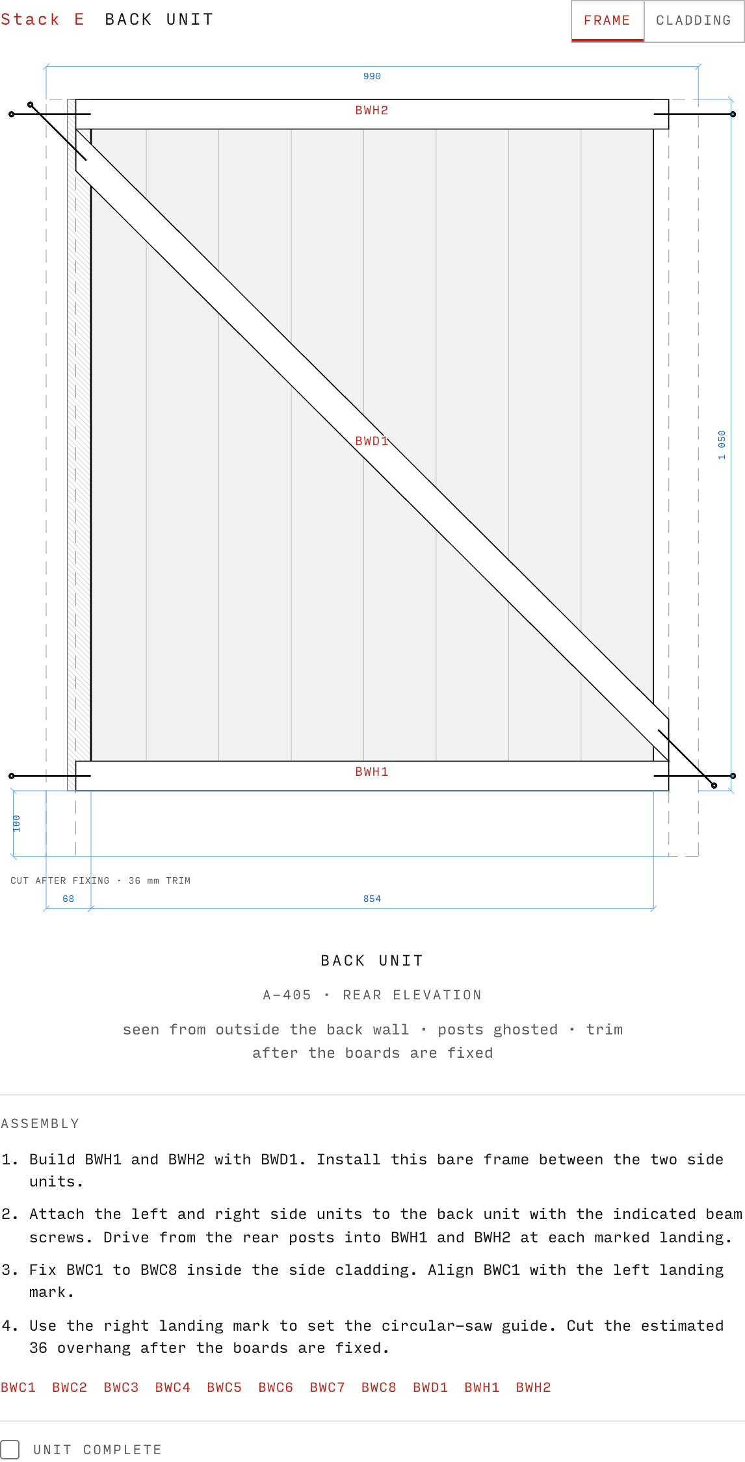
docs/verification/guide/shots/unit-e-1440.png
