feelepxyz/dass/docs/verification/guide/shots/unit-g-1440.png

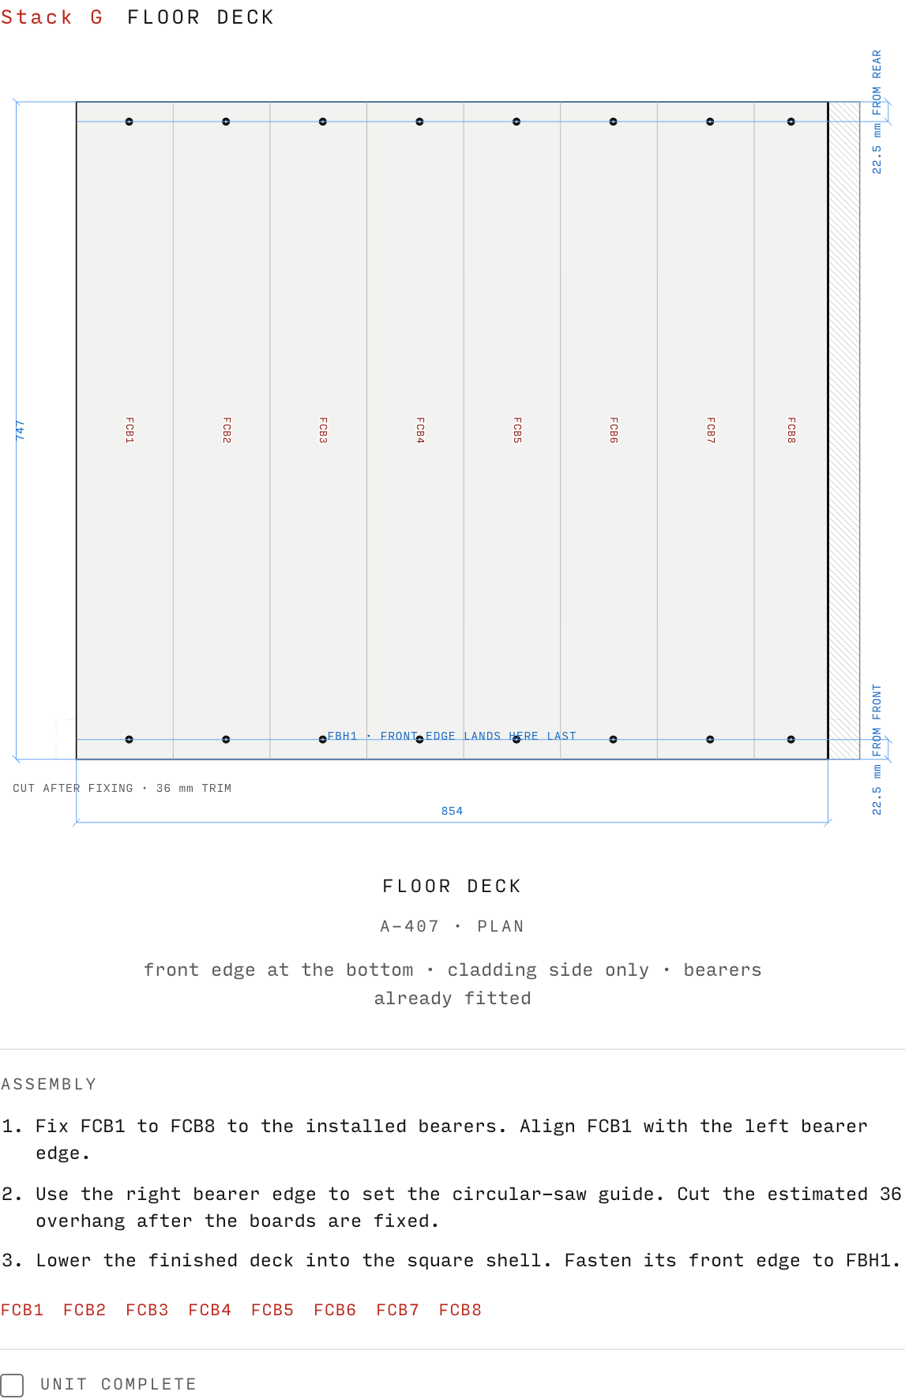
docs/verification/guide/shots/unit-g-1440.png
