feelepxyz/dass/docs/verification/guide/shots/unit-h-1440.png

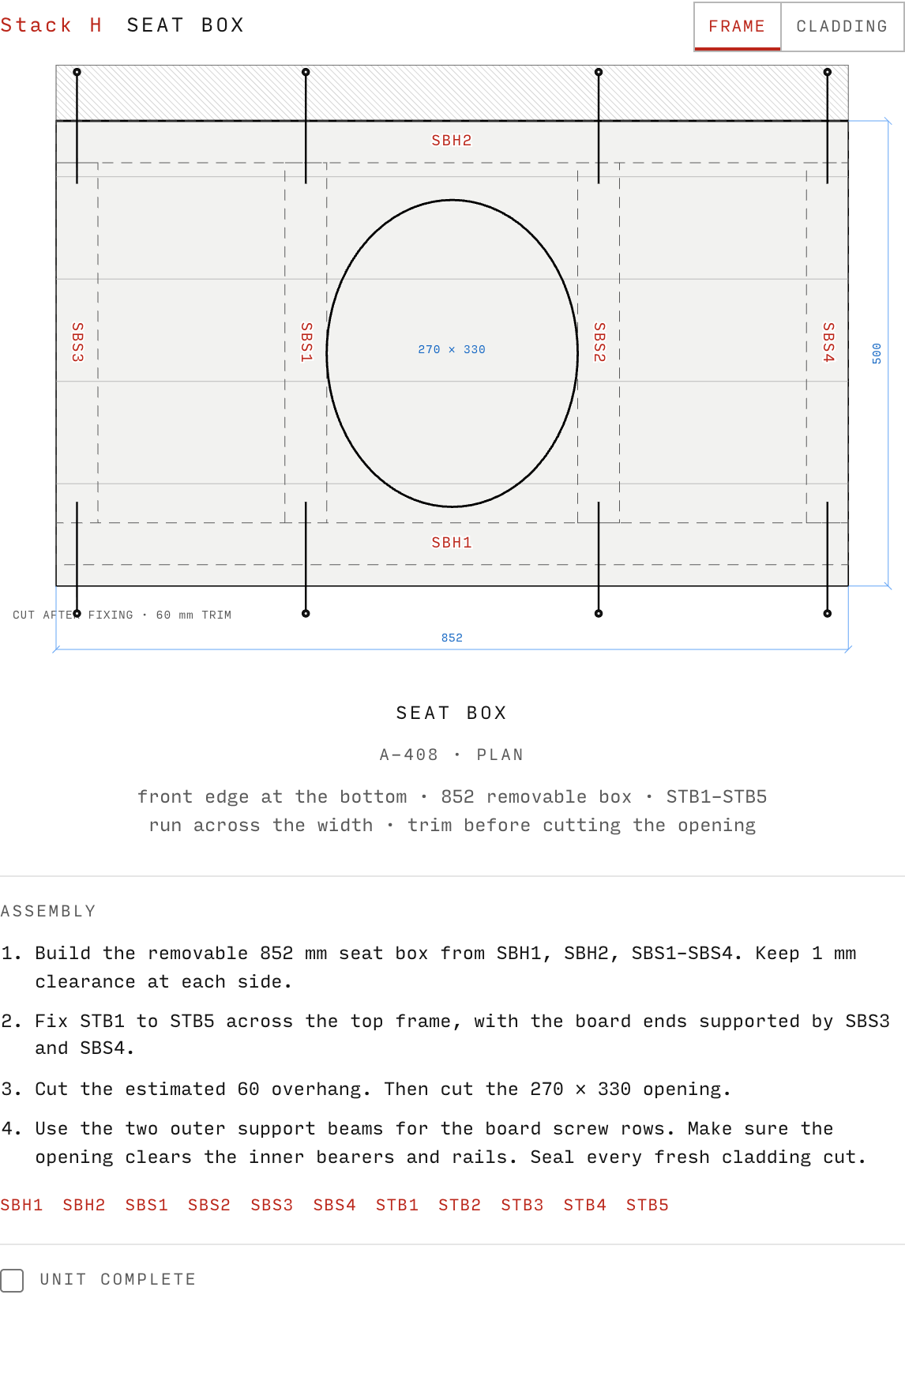
docs/verification/guide/shots/unit-h-1440.png
