feelepxyz/dass/docs/verification/guide/shots/unit-h-cladding-1440.png

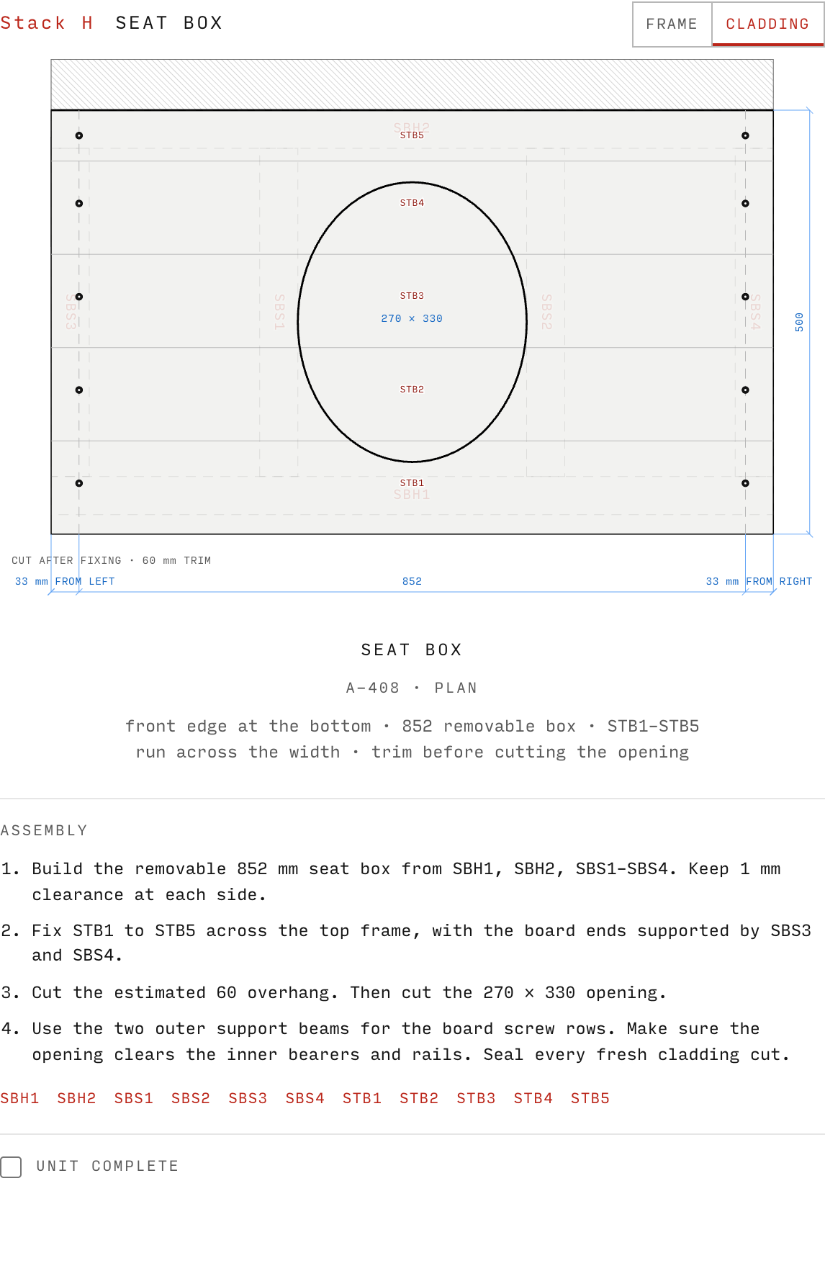
docs/verification/guide/shots/unit-h-cladding-1440.png
