feelepxyz/dass/docs/verification/guide/shots/unit-i-1440.png

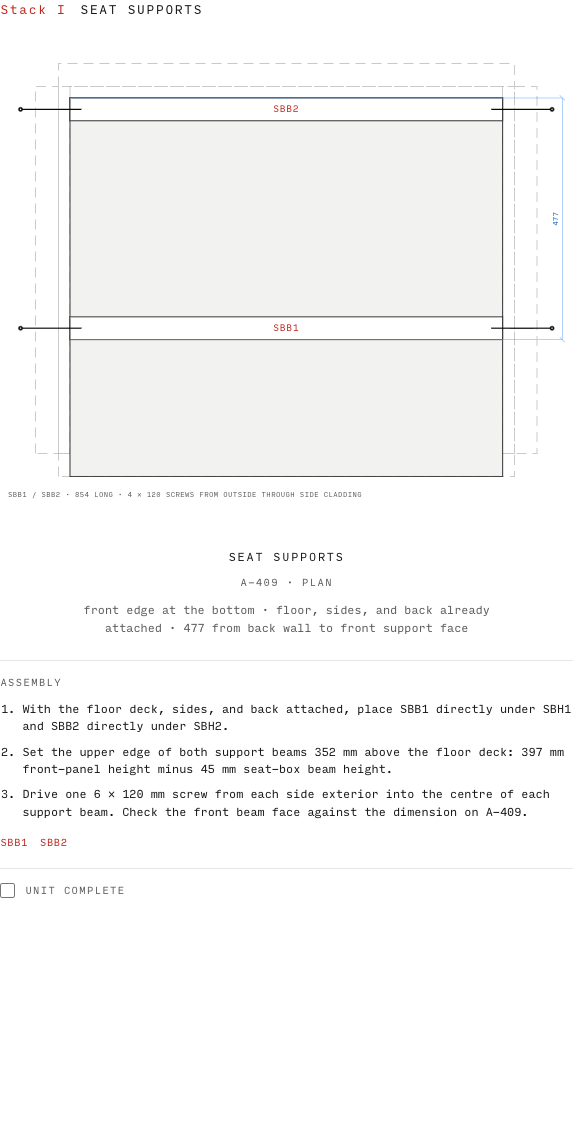
docs/verification/guide/shots/unit-i-1440.png
