feelepxyz/dass/docs/verification/guide/shots/unit-j-1440.png

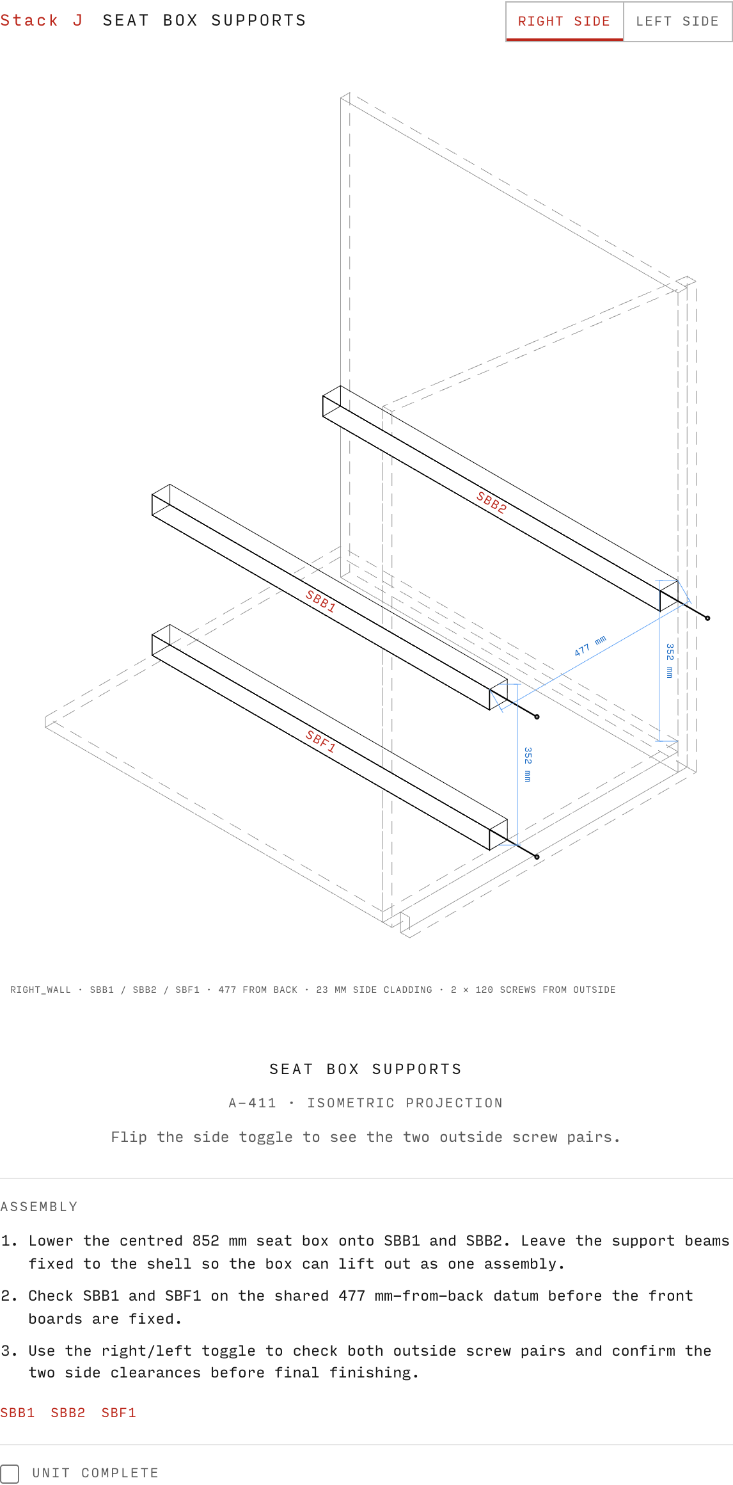
docs/verification/guide/shots/unit-j-1440.png
