feelepxyz/dass/docs/verification/guide/shots/unit-j-left-1440.png

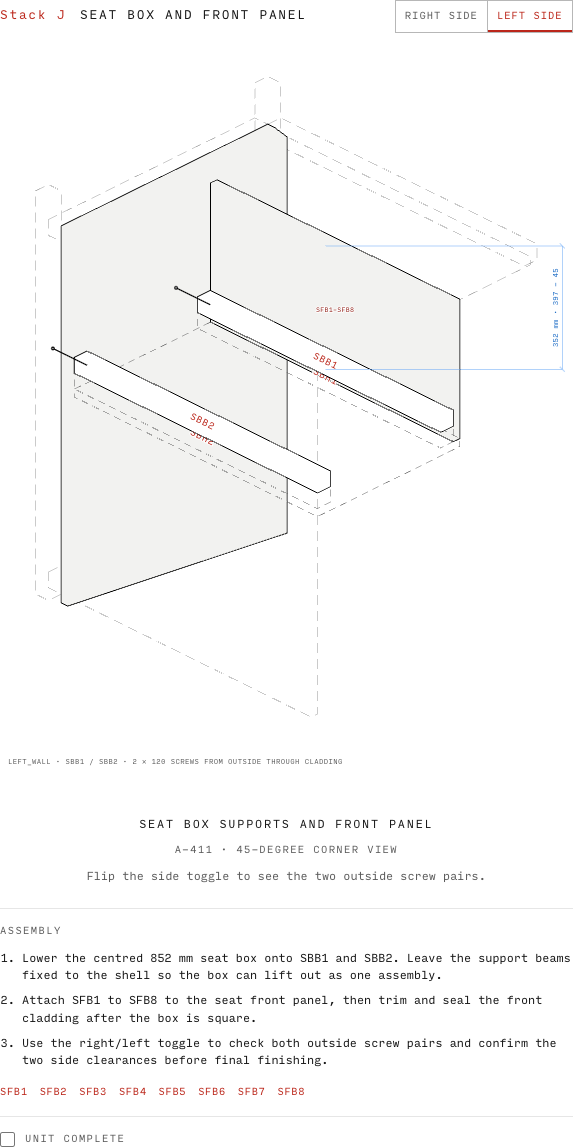
docs/verification/guide/shots/unit-j-left-1440.png
