feelepxyz/dass/docs/verification/guide/shots/unit-k-1440.png

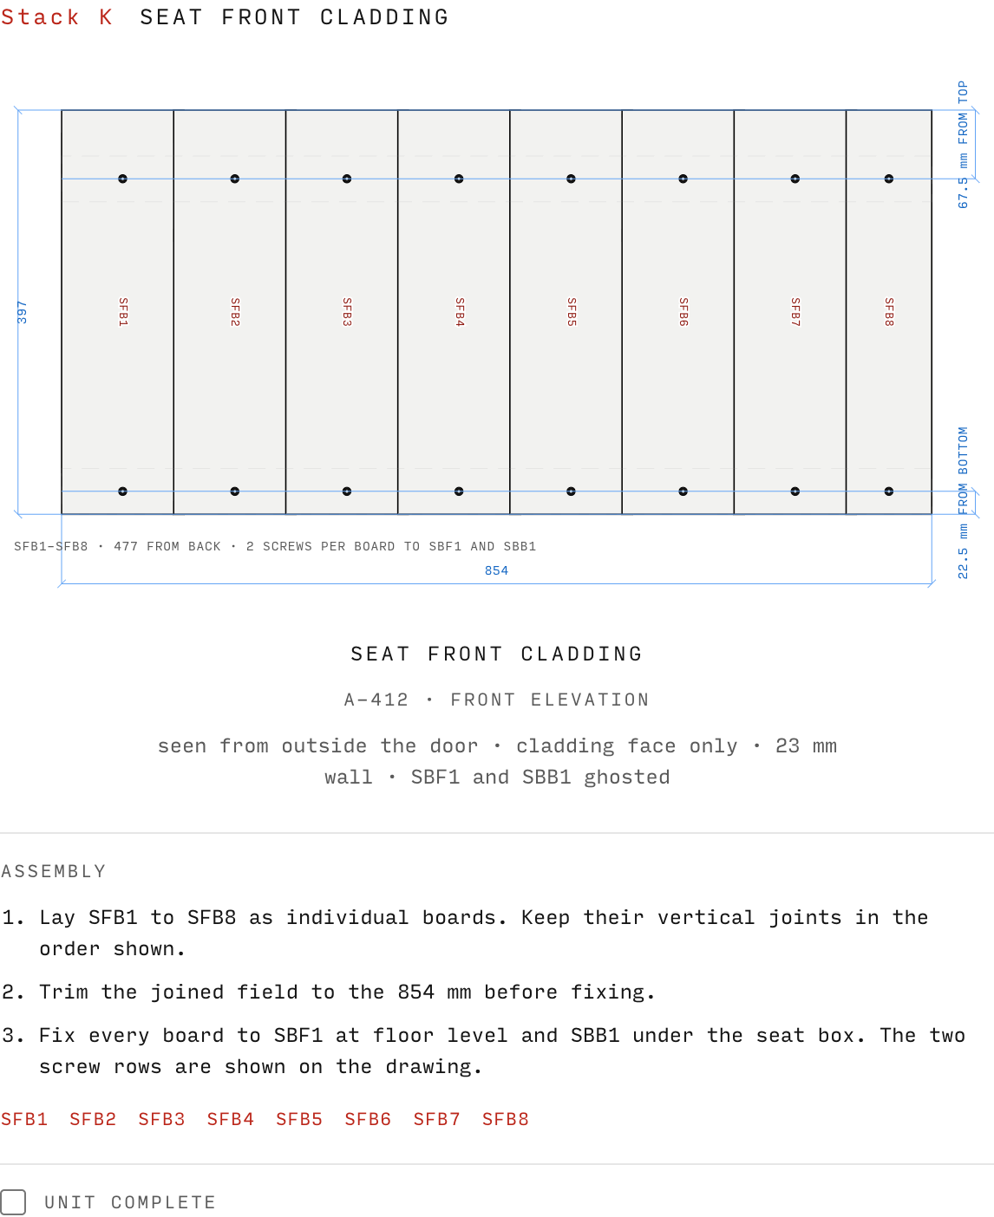
docs/verification/guide/shots/unit-k-1440.png
