feelepxyz/dass/docs/verification/guide/shots/viewer-1440.png

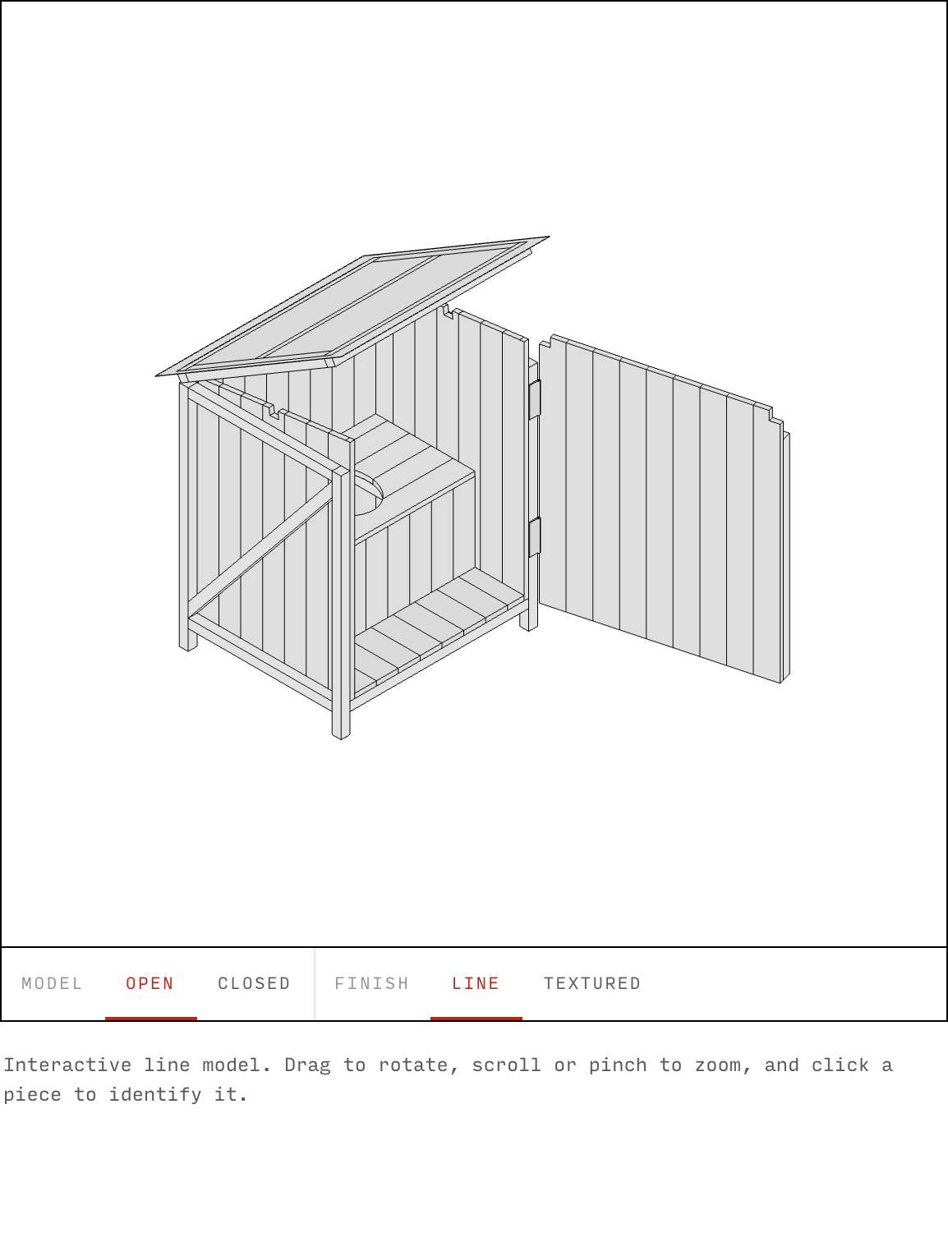
docs/verification/guide/shots/viewer-1440.png
