feelepxyz/dass/docs/verification/guide/shots/viewer-line-tone-mapping.png

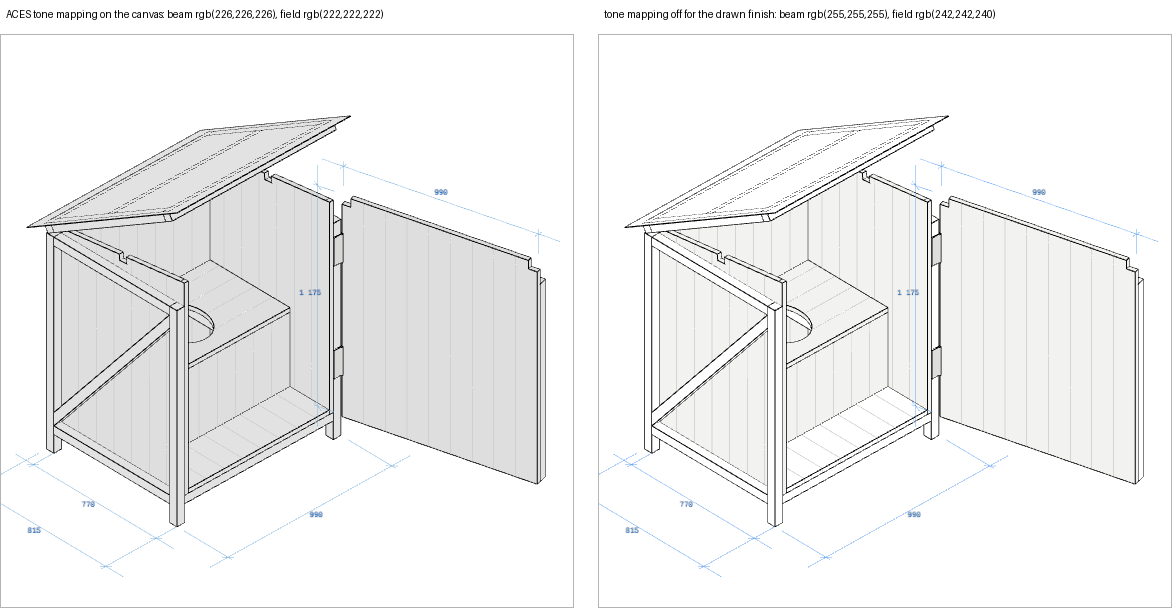
docs/verification/guide/shots/viewer-line-tone-mapping.png
