feelepxyz/dass/docs/verification/guide/shots/viewer-picked.png

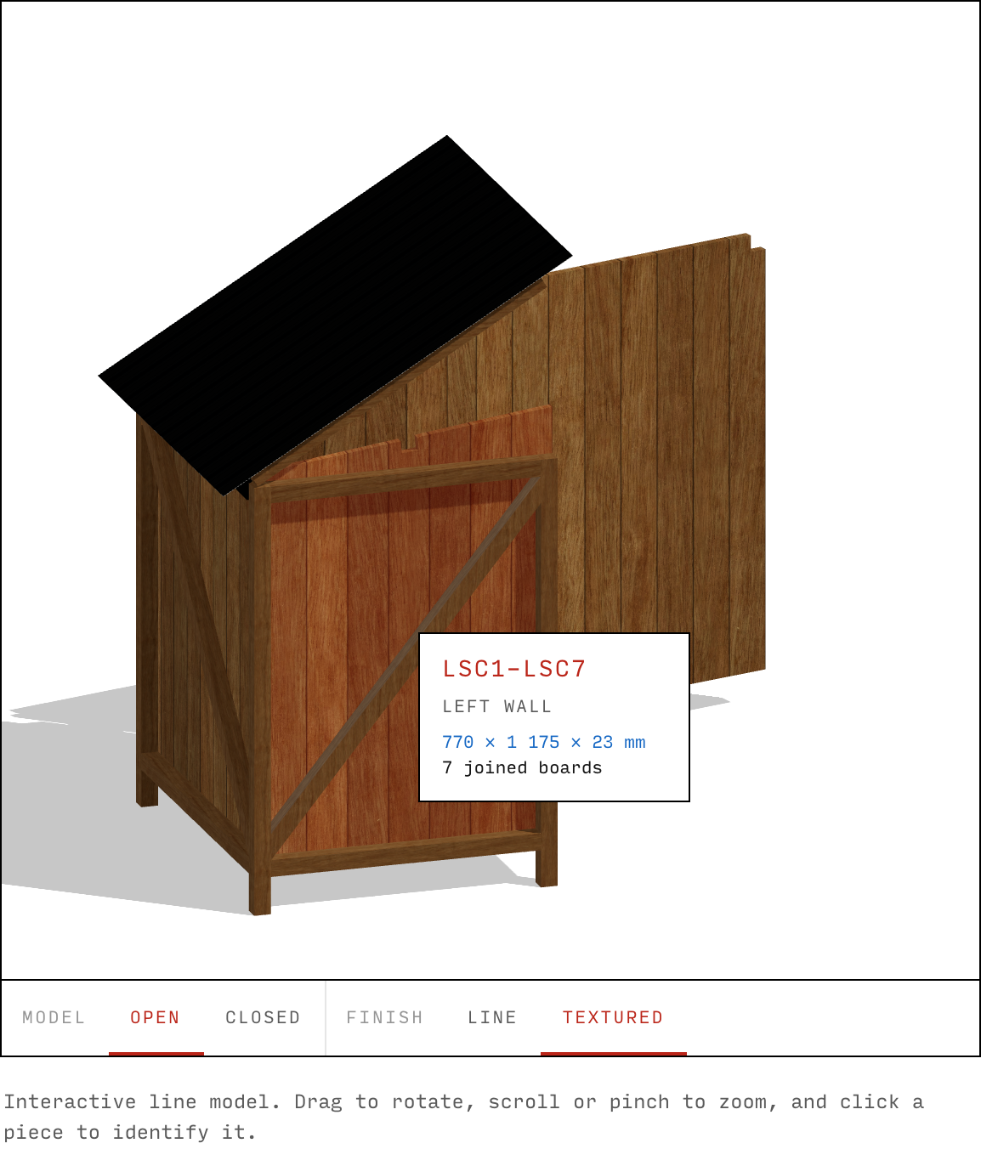
docs/verification/guide/shots/viewer-picked.png
