feelepxyz/dass/docs/verification/guide/shots/views-390.png

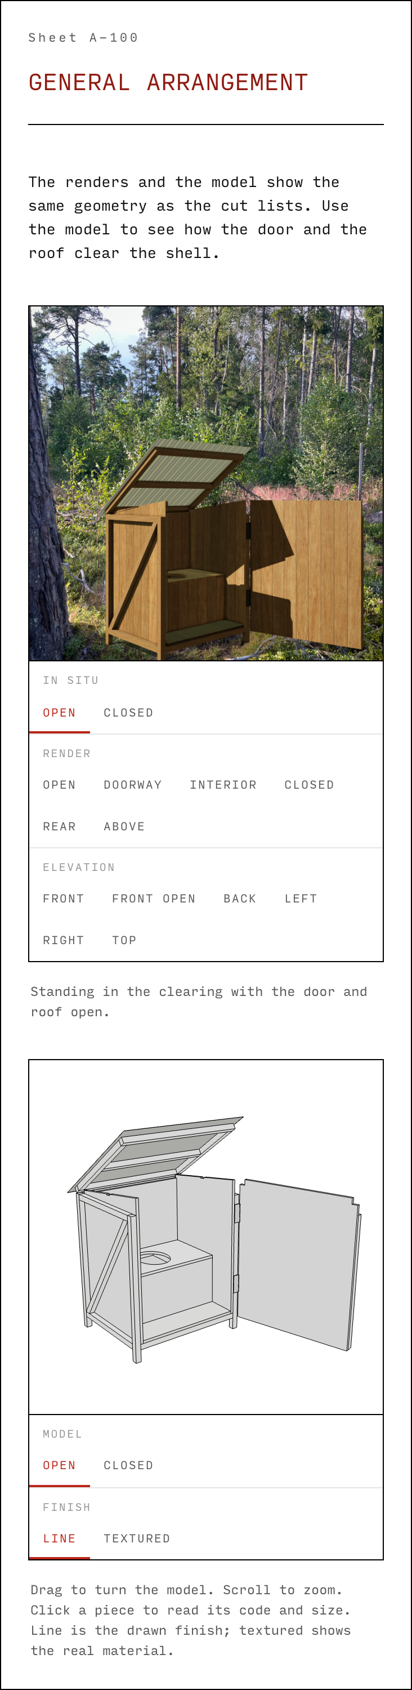
docs/verification/guide/shots/views-390.png
