feelepxyz/dass/docs/verification/guide/shots/views-1440.png

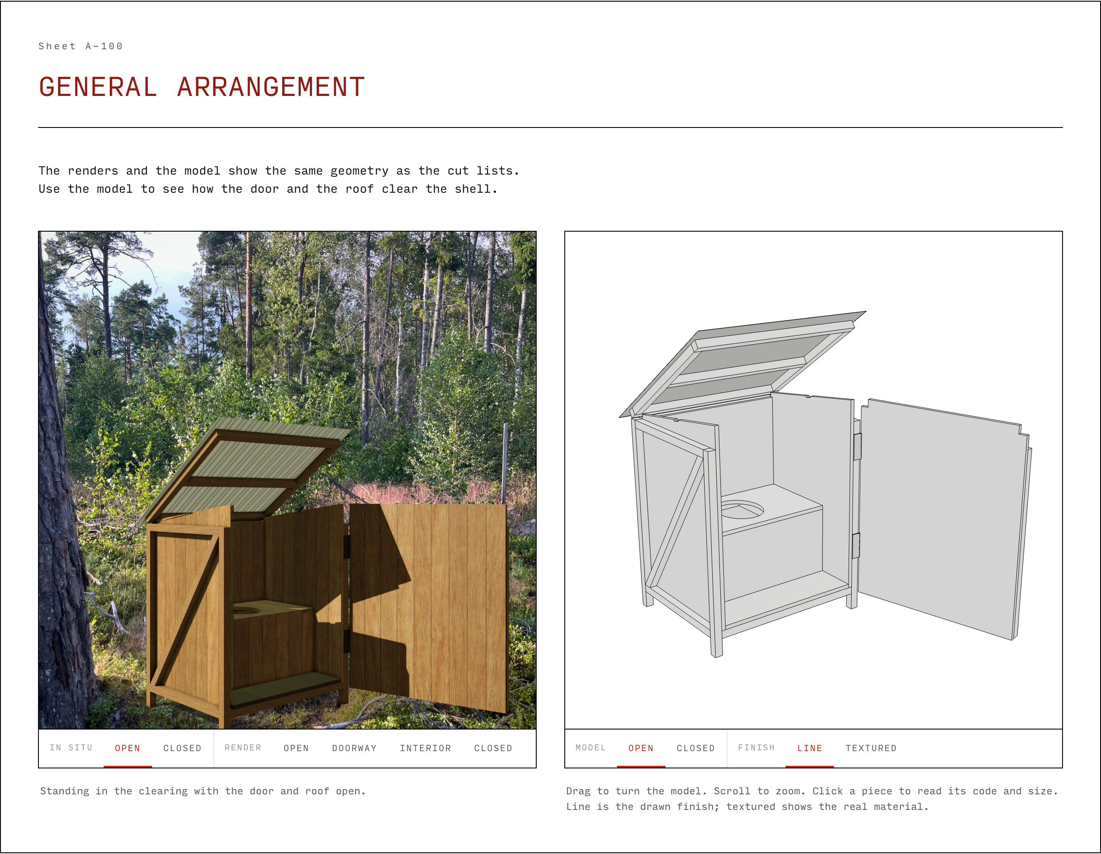
docs/verification/guide/shots/views-1440.png
