feelepxyz/dass/docs/verification/evolution/drawing-door-front.png

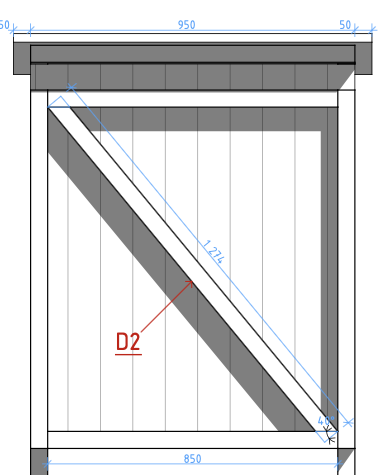
docs/verification/evolution/drawing-door-front.png
