feelepxyz/dass/docs/verification/evolution/drawing-seat-section.png

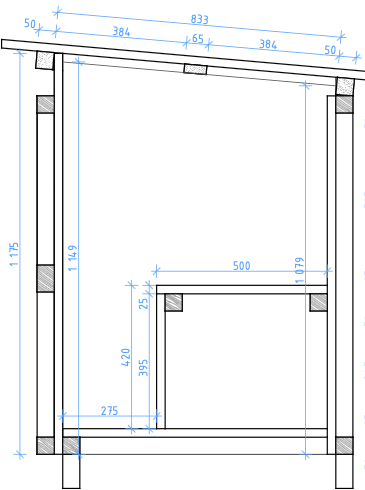
docs/verification/evolution/drawing-seat-section.png
