feelepxyz/dass/docs/verification/evolution/drawing-side-frame.png

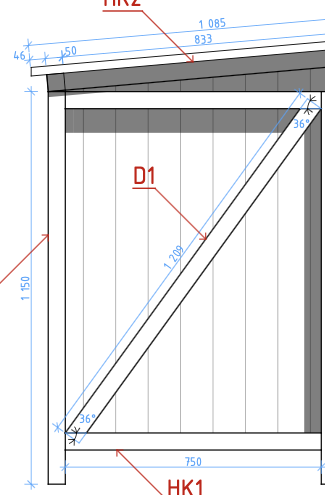
docs/verification/evolution/drawing-side-frame.png
