feelepxyz/dass/docs/verification/evolution/render-door-front.png

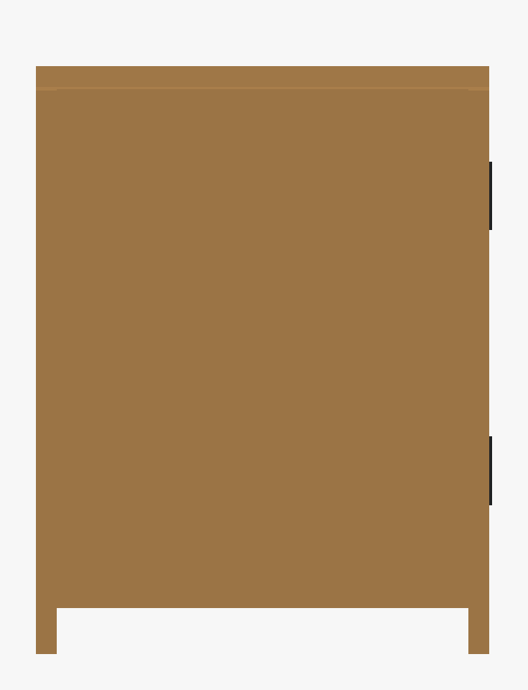
docs/verification/evolution/render-door-front.png
