feelepxyz/dass/docs/verification/evolution/render-seat-section.png

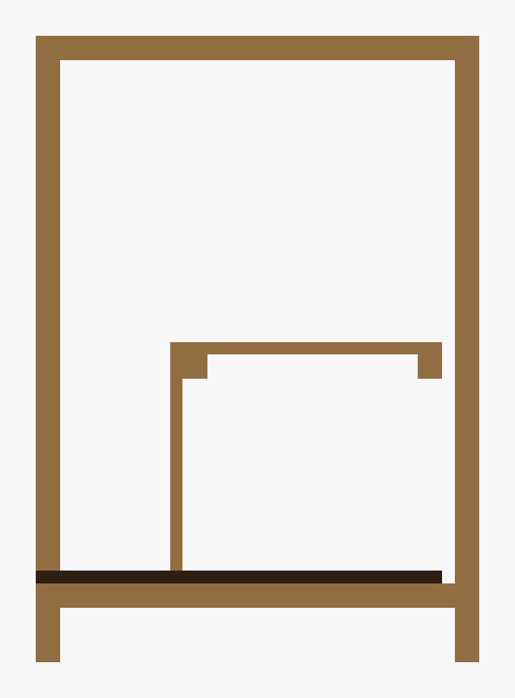
docs/verification/evolution/render-seat-section.png
