feelepxyz/dass/docs/verification/geometry/alignment-final-closed-front_20260730T114928Z.png

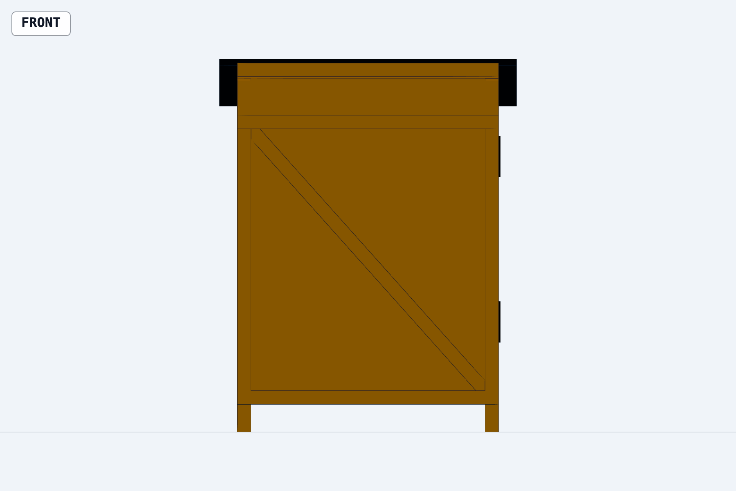
docs/verification/geometry/alignment-final-closed-front_20260730T114928Z.png
