feelepxyz/dass/docs/verification/geometry/alignment-final-closed-side_20260730T114928Z.png

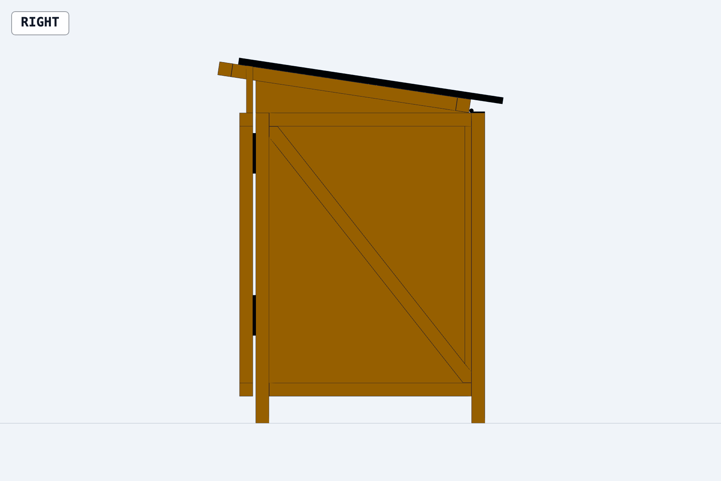
docs/verification/geometry/alignment-final-closed-side_20260730T114928Z.png
