feelepxyz/dass/docs/verification/geometry/alignment-final-open-opposite_20260730T114928Z.png

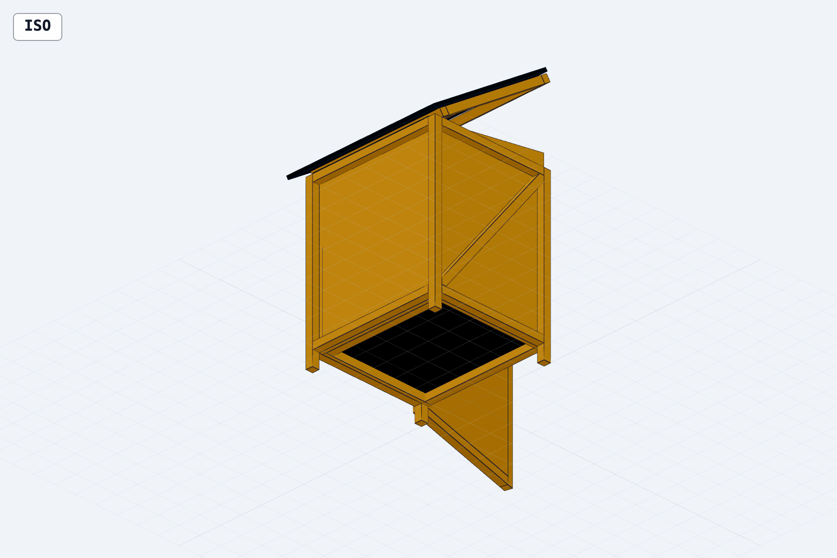
docs/verification/geometry/alignment-final-open-opposite_20260730T114928Z.png
