feelepxyz/dass/docs/verification/geometry/alignment-final-open-side_20260730T114928Z.png

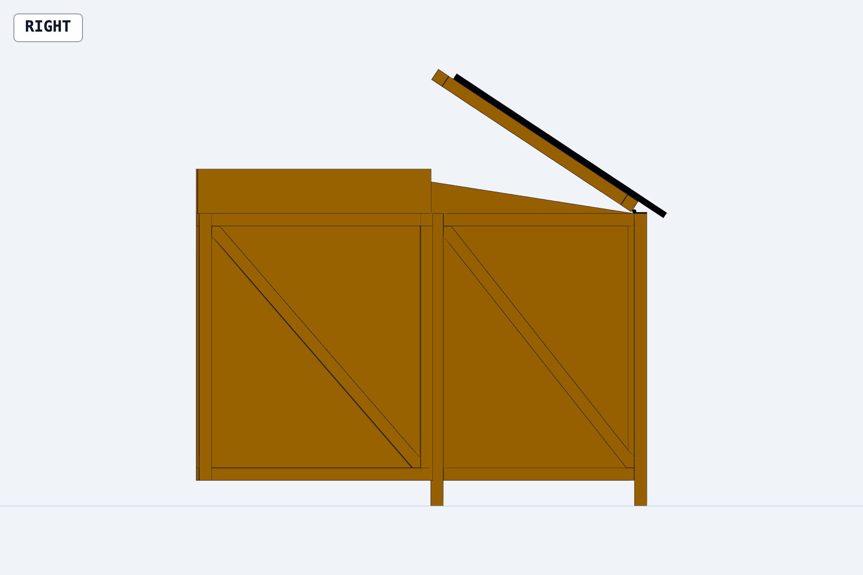
docs/verification/geometry/alignment-final-open-side_20260730T114928Z.png
