feelepxyz/dass/docs/verification/geometry/dass-closed-height-front_20260803T162044Z.png

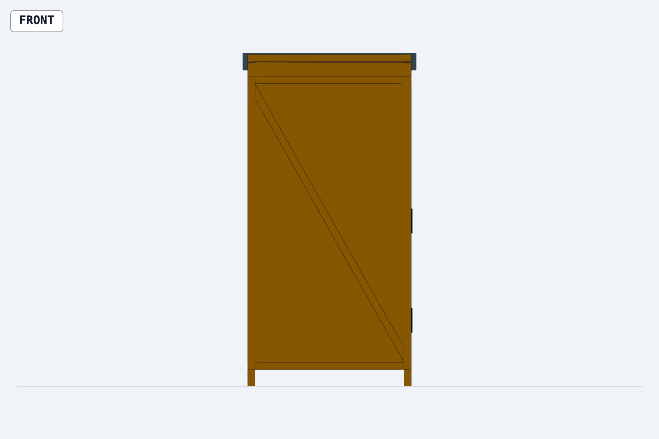
docs/verification/geometry/dass-closed-height-front_20260803T162044Z.png
