feelepxyz/dass/docs/verification/geometry/door-roof-closed-iso_20260730T120346Z.png

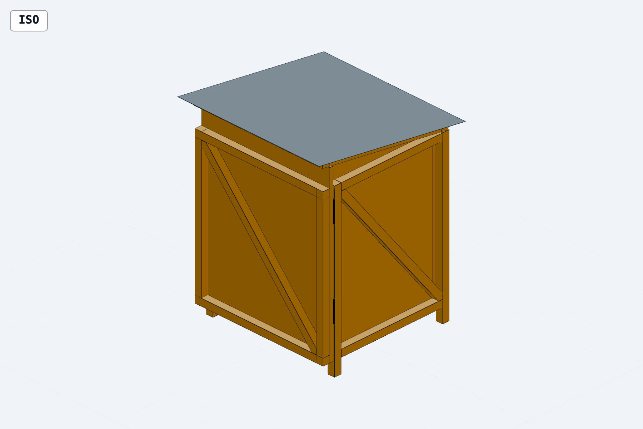
docs/verification/geometry/door-roof-closed-iso_20260730T120346Z.png
