feelepxyz/dass/docs/verification/geometry/hk1-hinges-front_20260730T111920Z.png

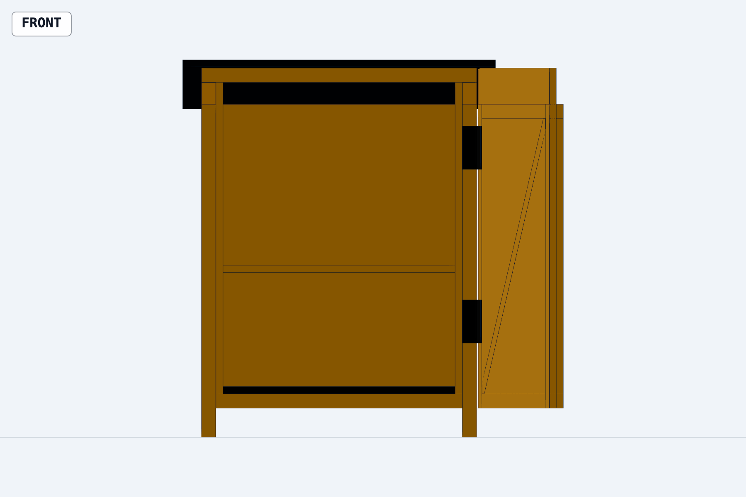
docs/verification/geometry/hk1-hinges-front_20260730T111920Z.png
