feelepxyz/dass/docs/verification/geometry/nits-closed-front_20260730T210105Z.png

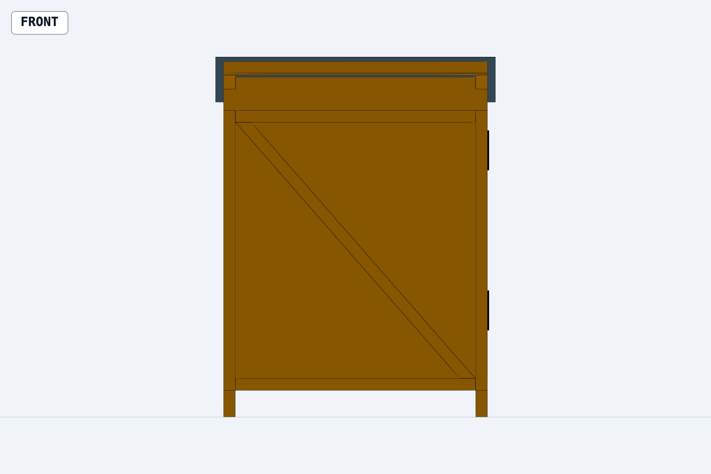
docs/verification/geometry/nits-closed-front_20260730T210105Z.png
