feelepxyz/dass/docs/verification/geometry/nits-closed-left_20260730T210105Z.png

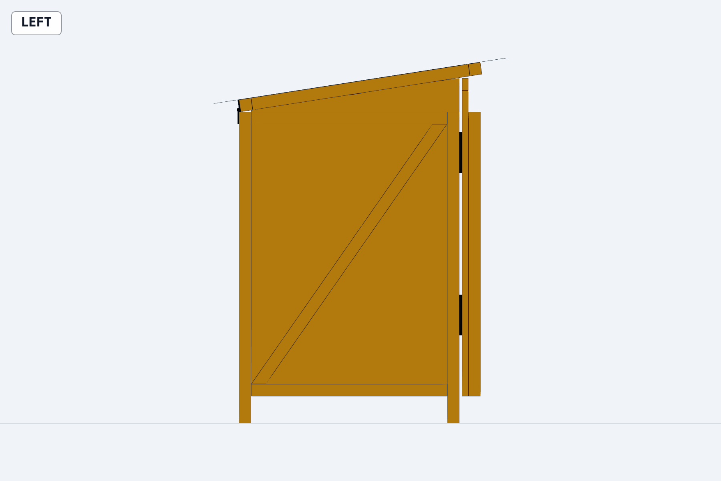
docs/verification/geometry/nits-closed-left_20260730T210105Z.png
