feelepxyz/dass/docs/verification/geometry/reconciled-final-top_20260730T111005Z.png

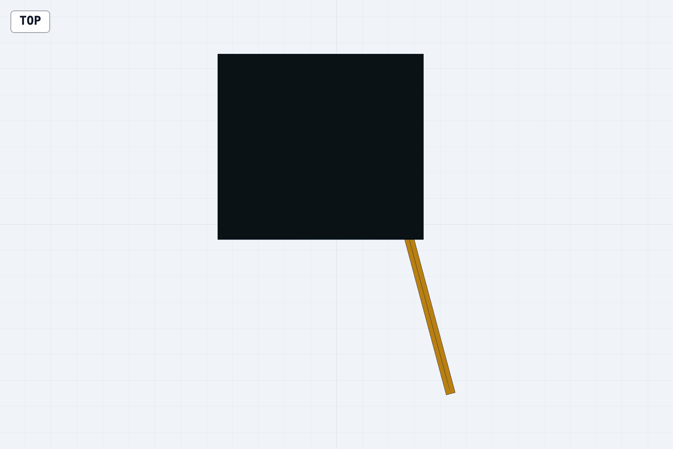
docs/verification/geometry/reconciled-final-top_20260730T111005Z.png
