feelepxyz/dass/docs/verification/geometry/review-top_20260730T115730Z.png

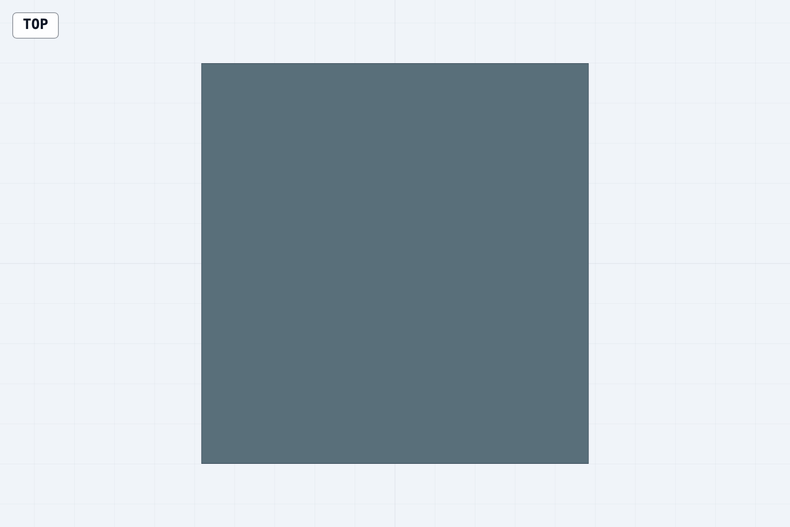
docs/verification/geometry/review-top_20260730T115730Z.png
