feelepxyz/dass/docs/verification/geometry/roof-final-closed-side_20260730T113342Z.png

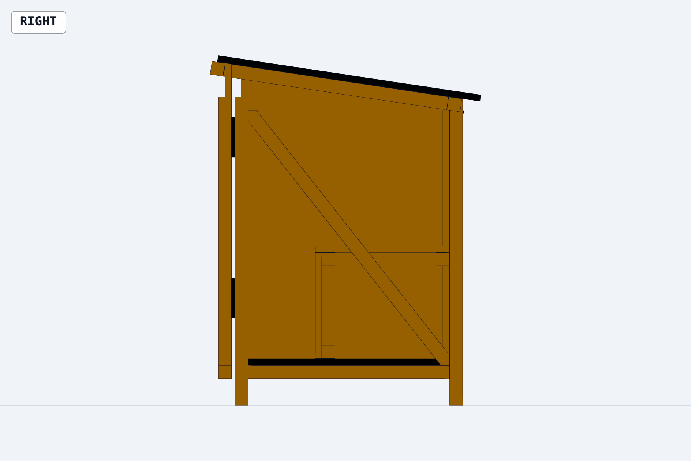
docs/verification/geometry/roof-final-closed-side_20260730T113342Z.png
