feelepxyz/dass/docs/verification/geometry/roof-frame-focus_20260730T113422Z.png

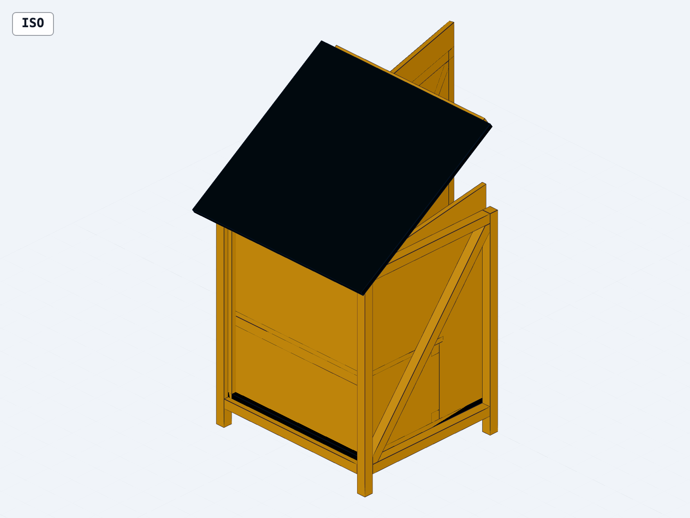
docs/verification/geometry/roof-frame-focus_20260730T113422Z.png
