feelepxyz/dass/docs/verification/geometry/seat-box-detail_20260802T100627Z.png

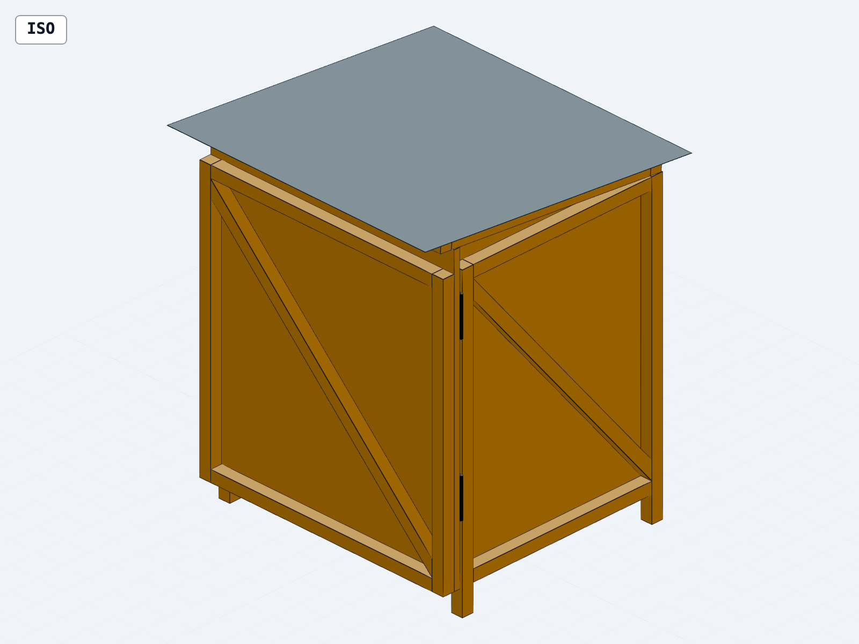
docs/verification/geometry/seat-box-detail_20260802T100627Z.png
