feelepxyz/dass/docs/verification/geometry/seat-box-open_20260802T100646Z.png

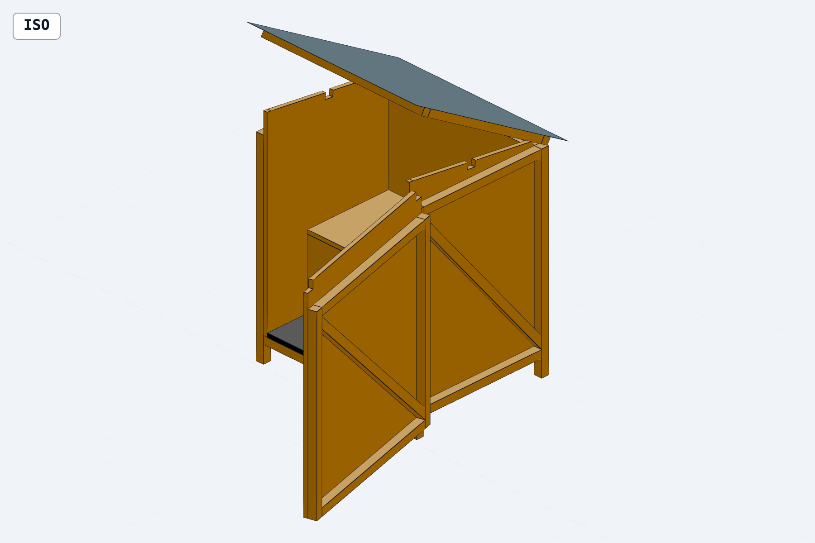
docs/verification/geometry/seat-box-open_20260802T100646Z.png
