feelepxyz/dass/docs/verification/geometry/seat-box-top_20260802T100700Z.png

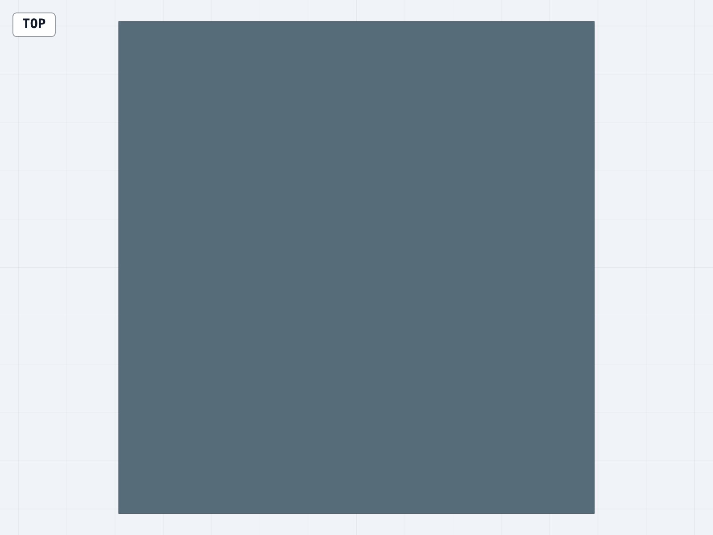
docs/verification/geometry/seat-box-top_20260802T100700Z.png
