feelepxyz/dass/docs/verification/geometry/seat-shell-opposite_20260802T072725Z.png

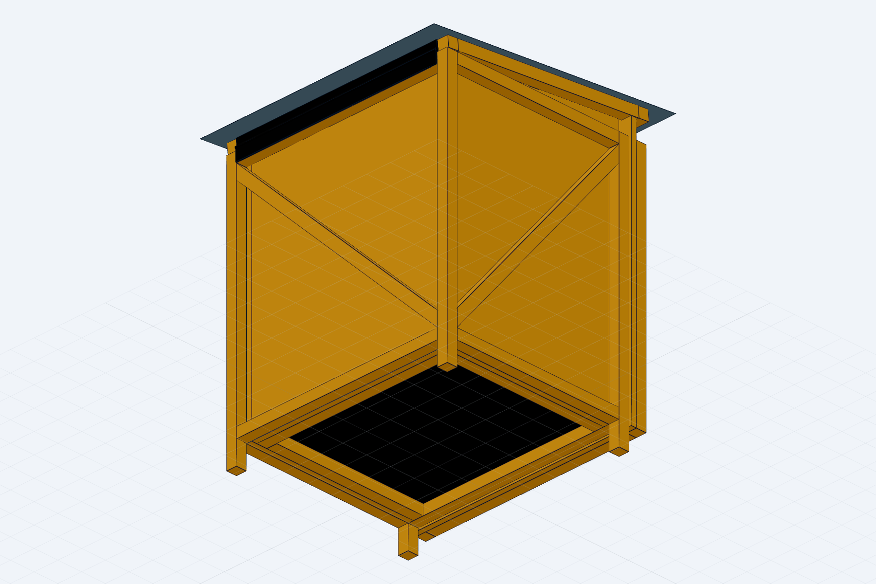
docs/verification/geometry/seat-shell-opposite_20260802T072725Z.png
