feelepxyz/dass/docs/verification/geometry/seat-support-open-top_20260802T080648Z.png

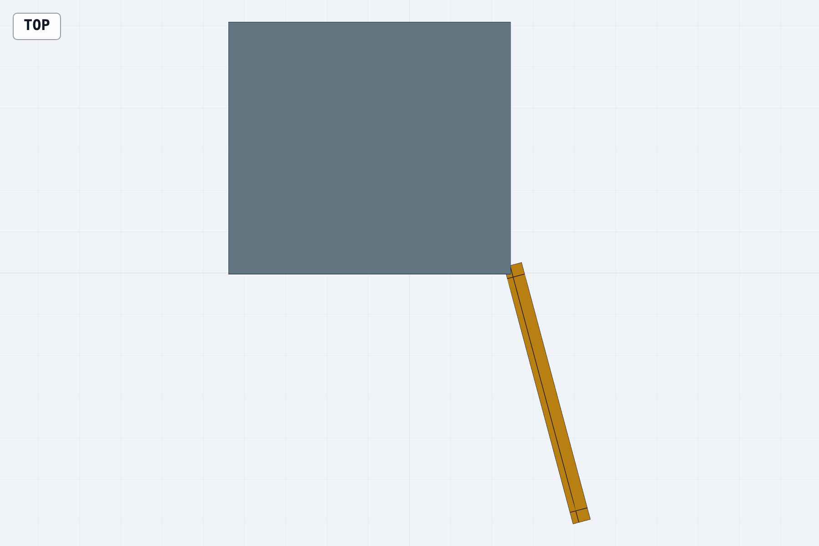
docs/verification/geometry/seat-support-open-top_20260802T080648Z.png
