feelepxyz/dass/docs/verification/geometry/validation-open-front_20260730T101611Z.png

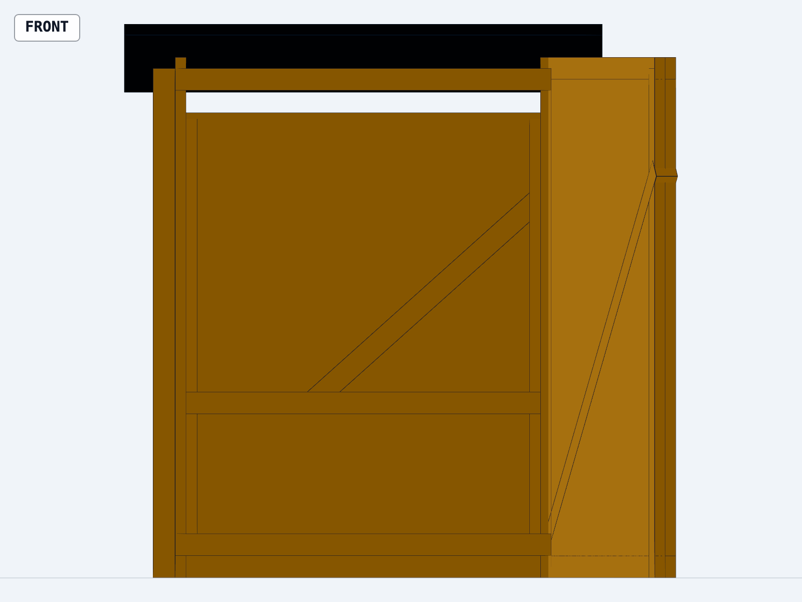
docs/verification/geometry/validation-open-front_20260730T101611Z.png
